EmiliaViaene/Un-designing-a-Thermal-Prediction-System/documentation/images/IMG_2420.jpg

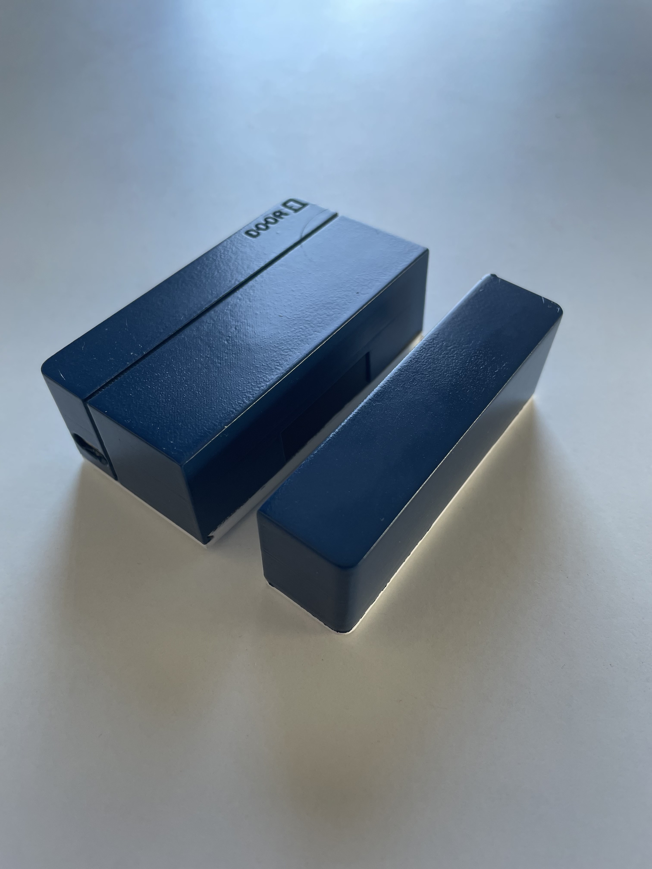
documentation/images/IMG_2420.jpg
