EmiliaViaene/Un-designing-a-Thermal-Prediction-System/documentation/images/IMG_2422.jpg

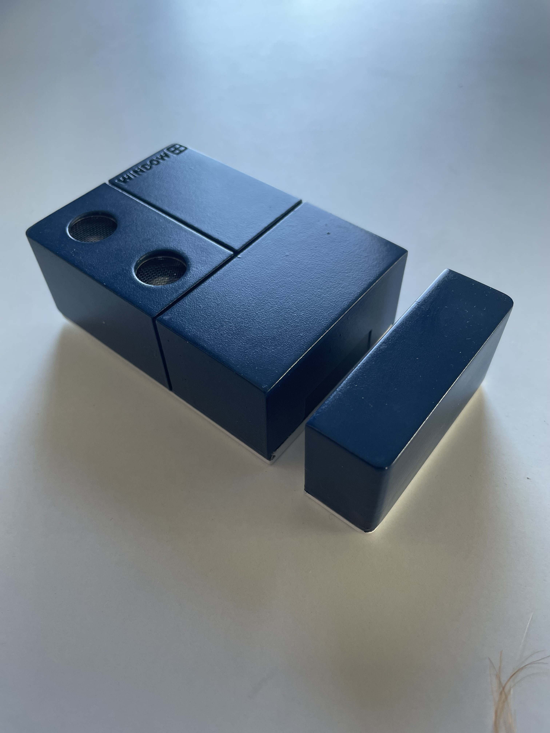
documentation/images/IMG_2422.jpg
