EmiliaViaene/Un-designing-a-Thermal-Prediction-System/documentation/images/IMG_2423.jpg

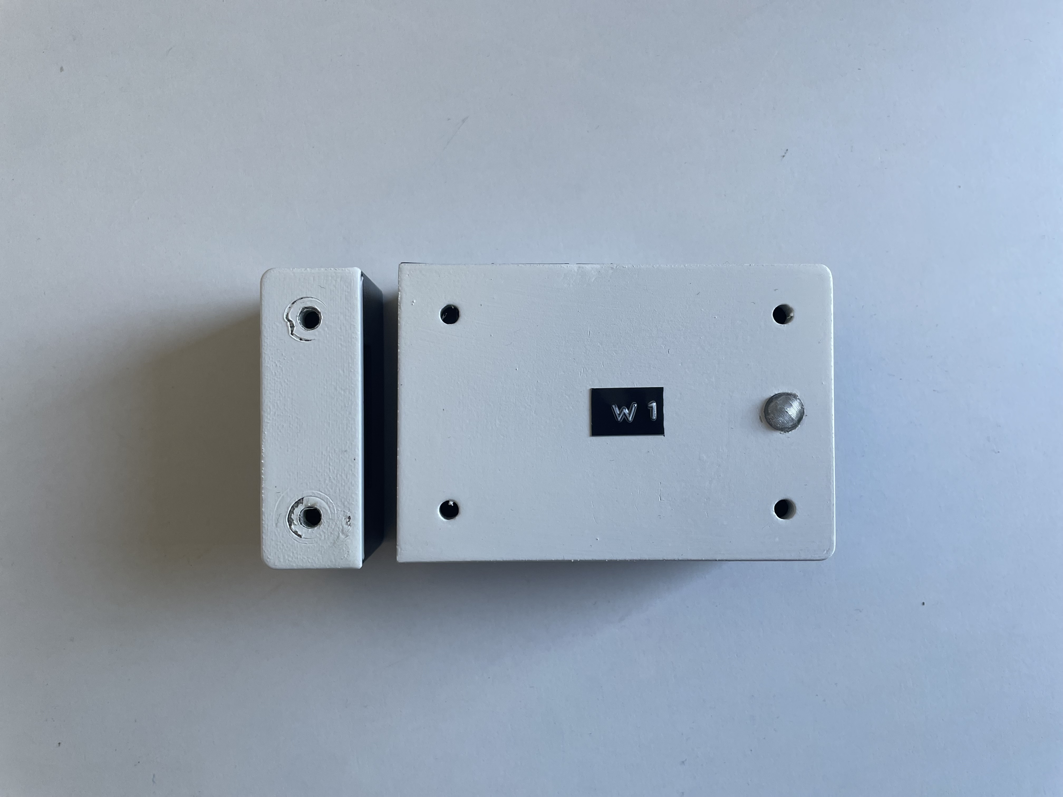
documentation/images/IMG_2423.jpg
