EmiliaViaene/Un-designing-a-Thermal-Prediction-System/documentation/images/IMG_2436.jpg

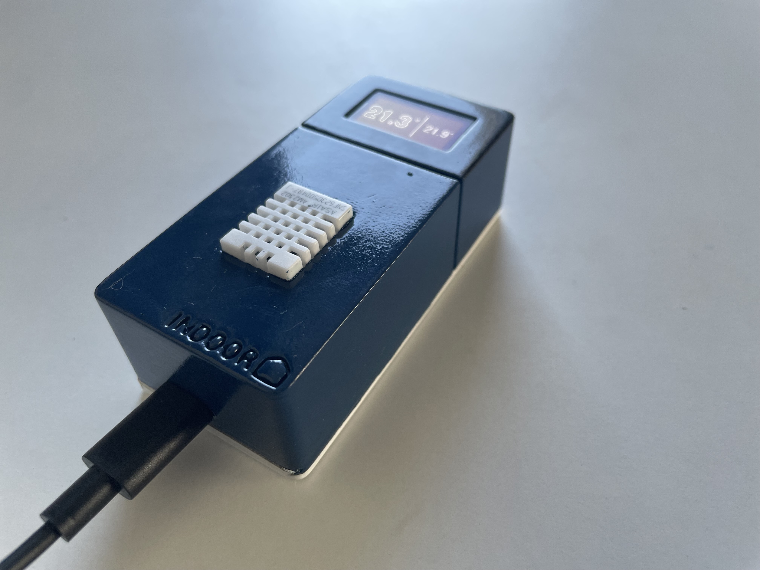
documentation/images/IMG_2436.jpg
