EmiliaViaene/Un-designing-a-Thermal-Prediction-System/documentation/images/IMG_2437.jpg

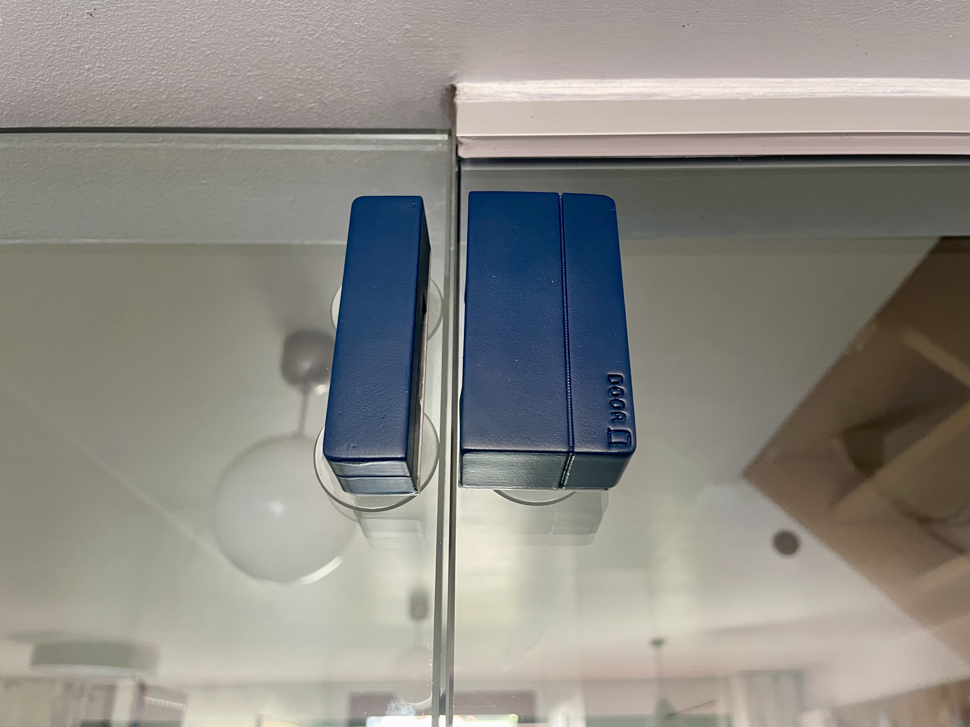
documentation/images/IMG_2437.jpg
