EmiliaViaene/Un-designing-a-Thermal-Prediction-System/documentation/images/IMG_2438.jpg

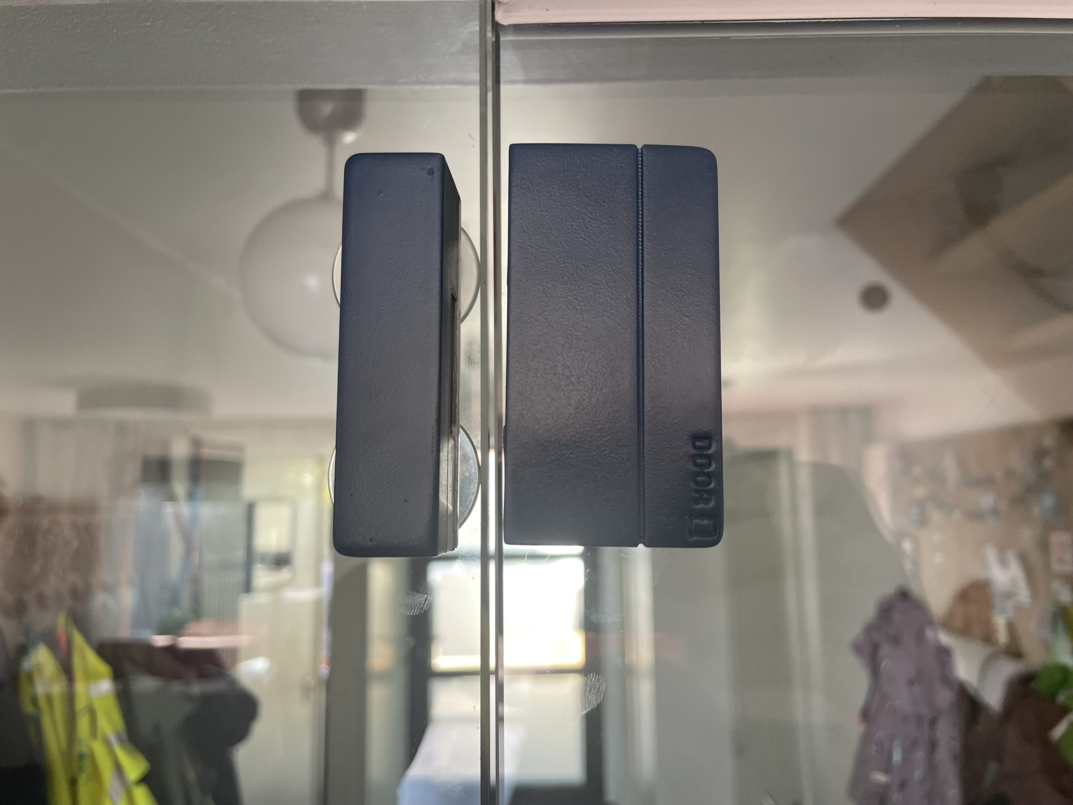
documentation/images/IMG_2438.jpg
