EmiliaViaene/Un-designing-a-Thermal-Prediction-System/documentation/images/IMG_2439.jpg

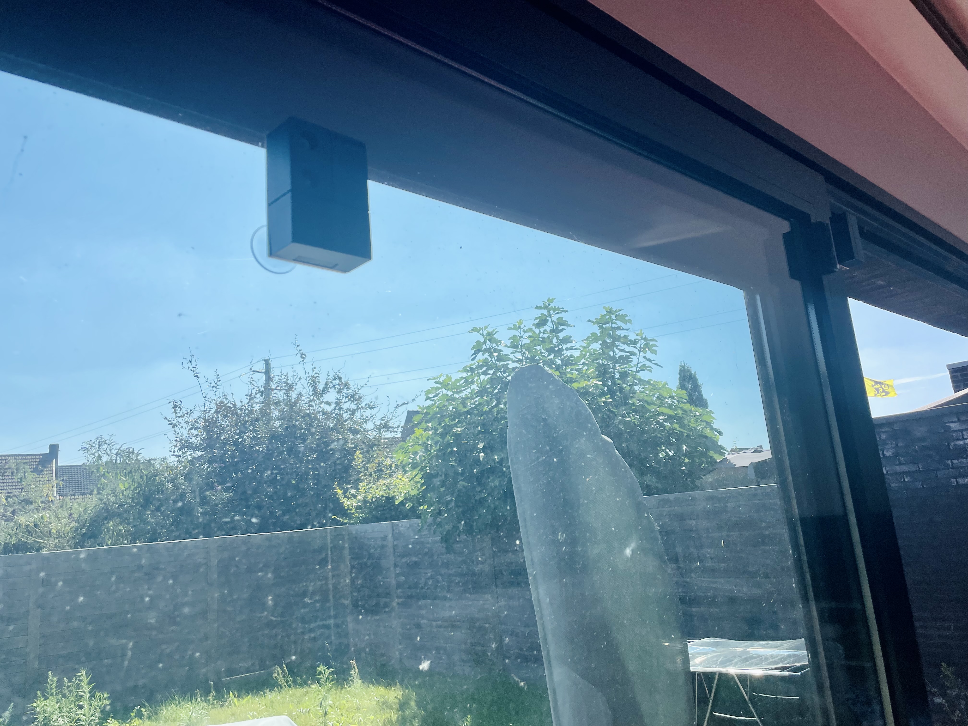
documentation/images/IMG_2439.jpg
