EmiliaViaene/Un-designing-a-Thermal-Prediction-System/documentation/images/IMG_2440.jpg

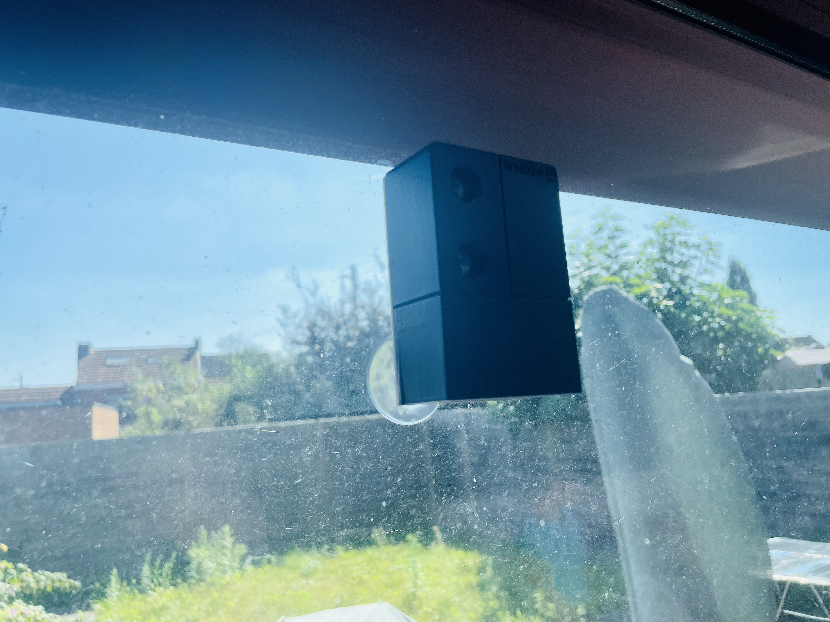
documentation/images/IMG_2440.jpg
