EmiliaViaene/Un-designing-a-Thermal-Prediction-System/documentation/images/IMG_2441.jpg

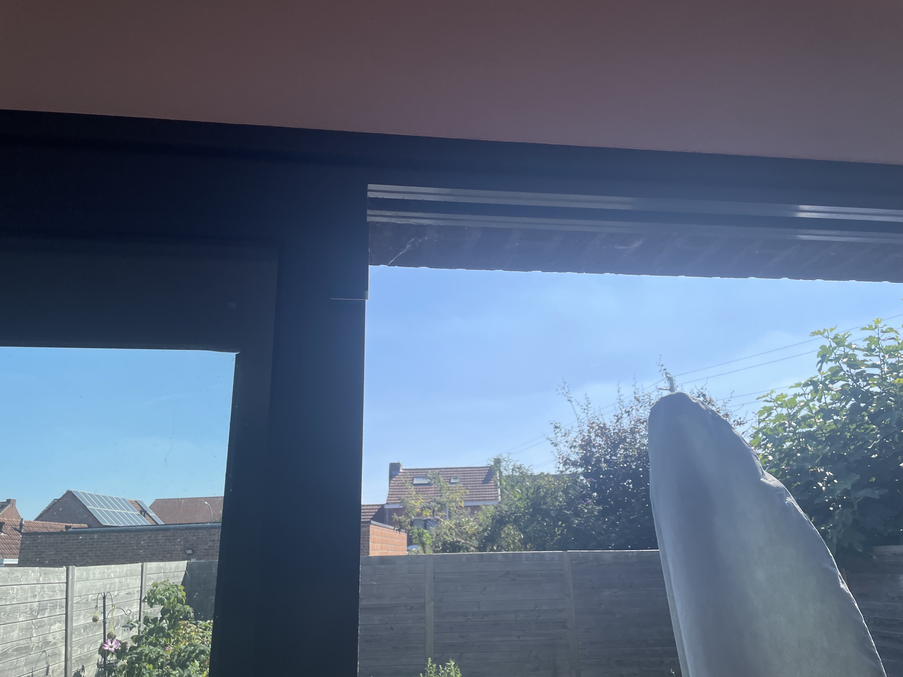
documentation/images/IMG_2441.jpg
