EmiliaViaene/Un-designing-a-Thermal-Prediction-System/documentation/images/IMG_2443.jpg

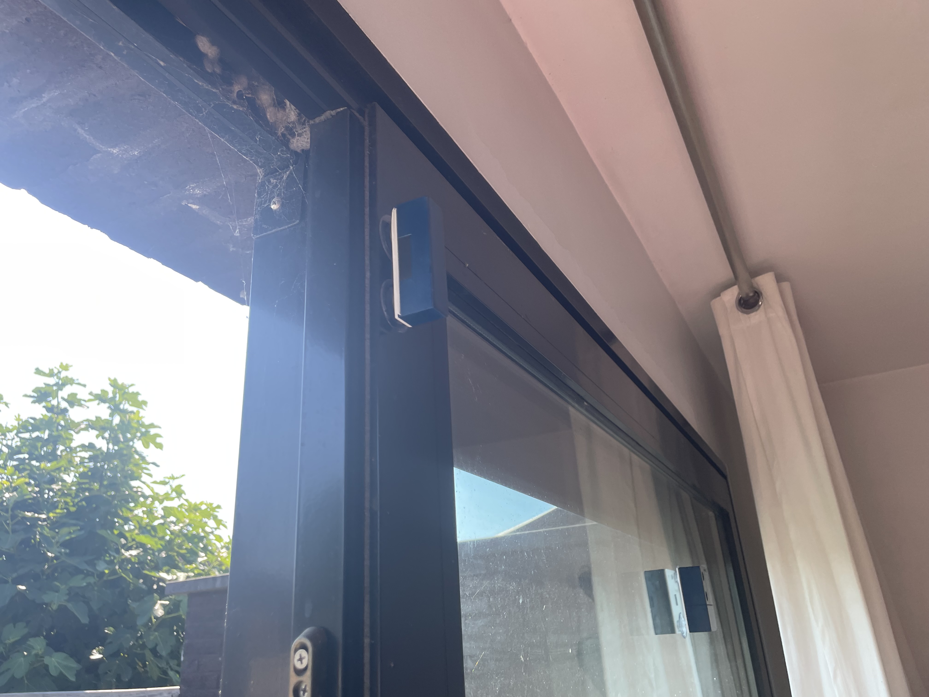
documentation/images/IMG_2443.jpg
