EmiliaViaene/Un-designing-a-Thermal-Prediction-System/documentation/images/IMG_2444.jpg

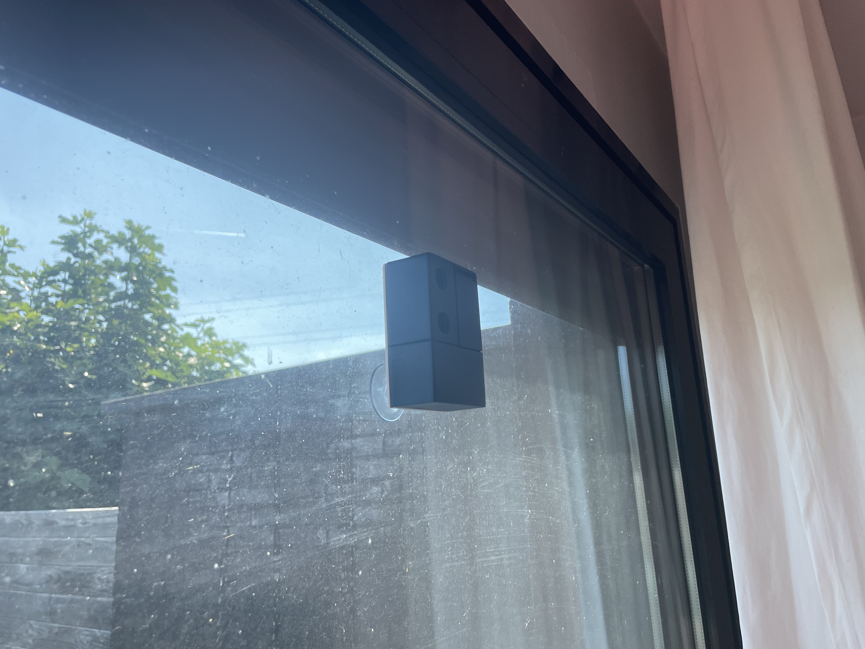
documentation/images/IMG_2444.jpg
