EmiliaViaene/Un-designing-a-Thermal-Prediction-System/documentation/images/IMG_2445.jpg

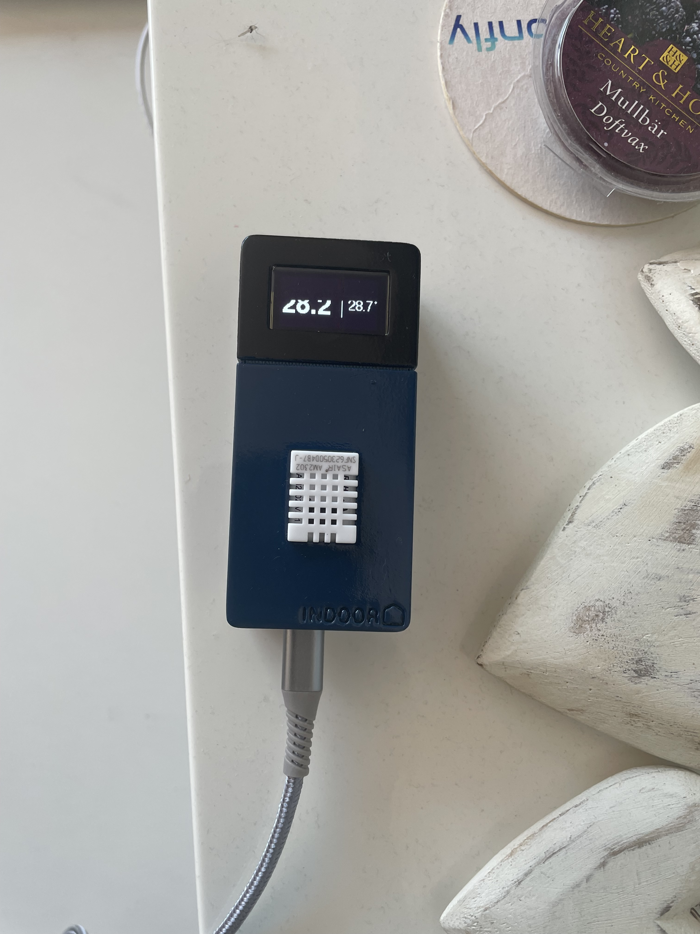
documentation/images/IMG_2445.jpg
