EmiliaViaene/Un-designing-a-Thermal-Prediction-System/documentation/images/IMG_2470.jpg

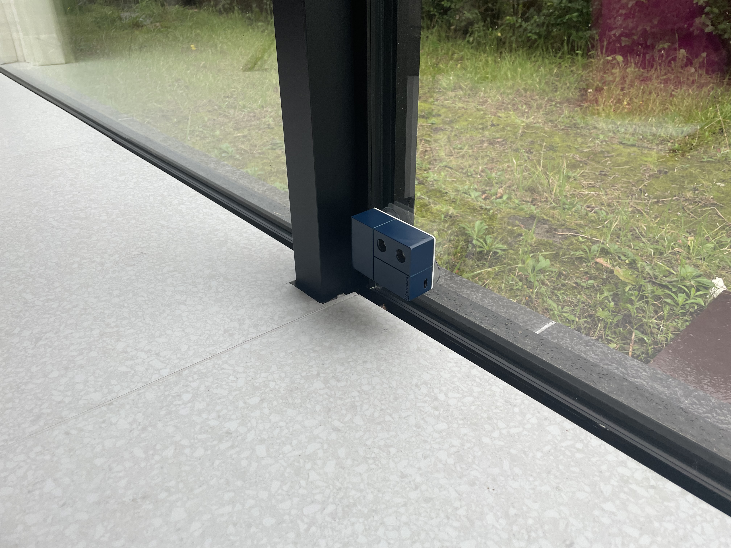
documentation/images/IMG_2470.jpg
