EmiliaViaene/Un-designing-a-Thermal-Prediction-System/documentation/images/IMG_2471.jpg

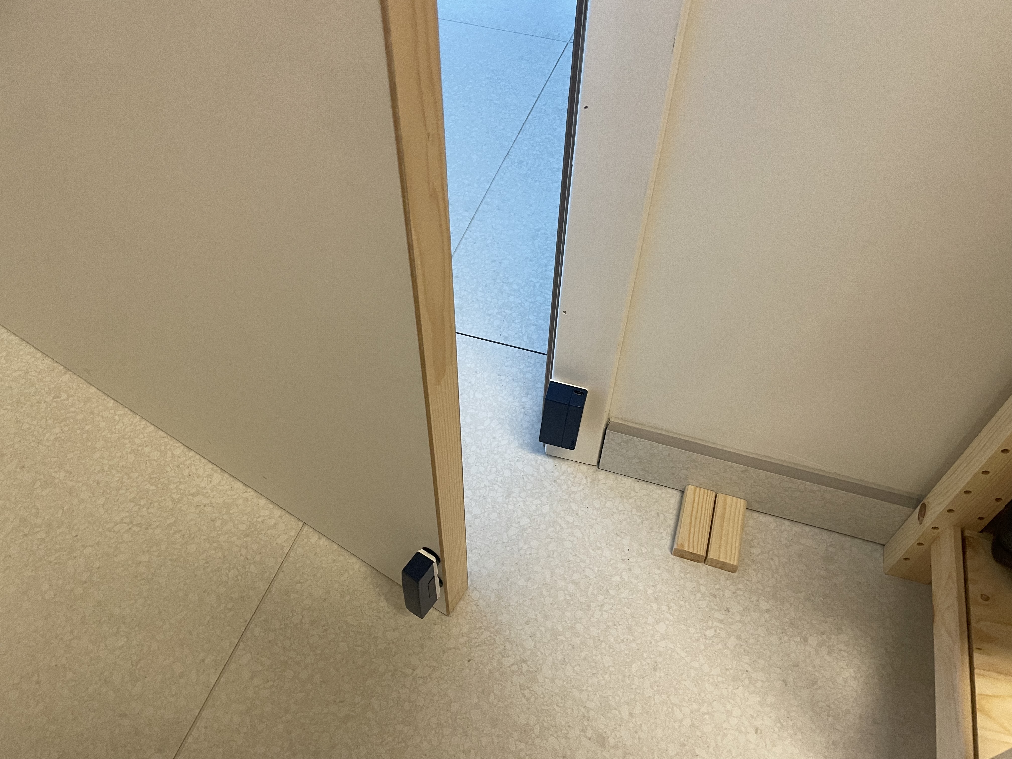
documentation/images/IMG_2471.jpg
