EmiliaViaene/Un-designing-a-Thermal-Prediction-System/documentation/images/IMG_2472.jpg

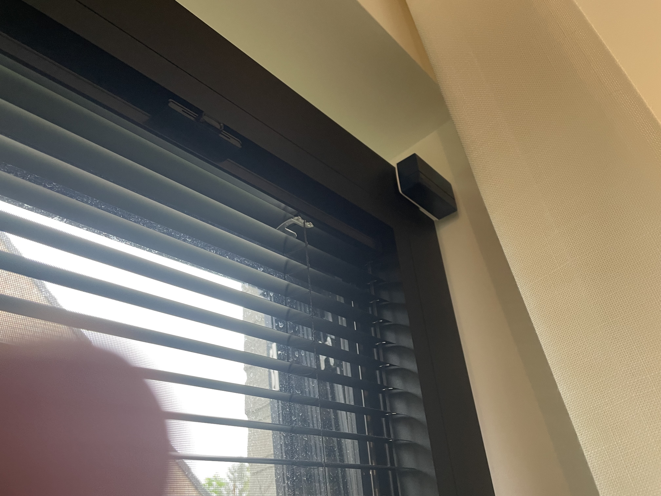
documentation/images/IMG_2472.jpg
