EmiliaViaene/Un-designing-a-Thermal-Prediction-System/documentation/images/IMG_2473.jpg

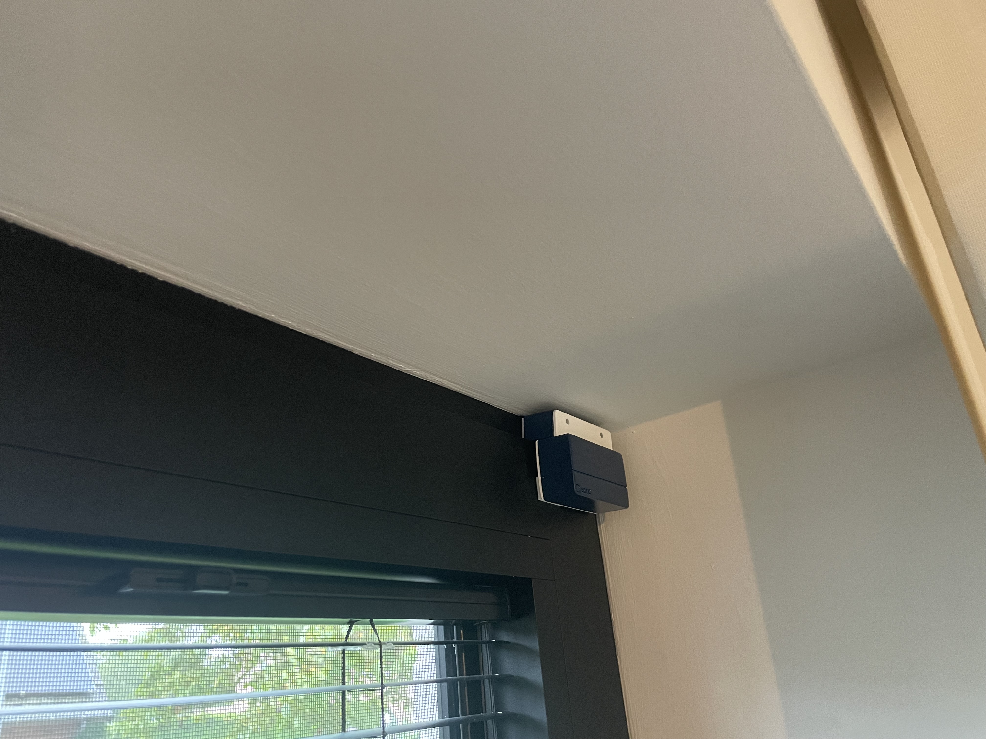
documentation/images/IMG_2473.jpg
