EmiliaViaene/Un-designing-a-Thermal-Prediction-System/documentation/images/IMG_2474.jpg

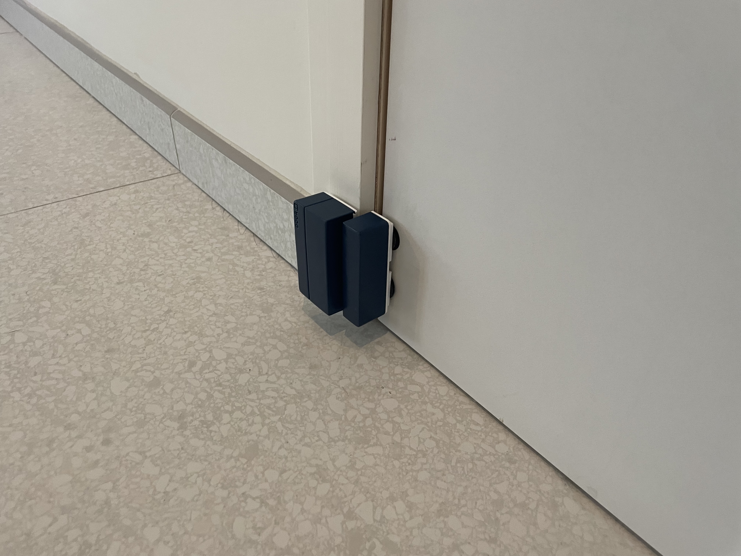
documentation/images/IMG_2474.jpg
