EmiliaViaene/Un-designing-a-Thermal-Prediction-System/documentation/images/IMG_2487.jpg

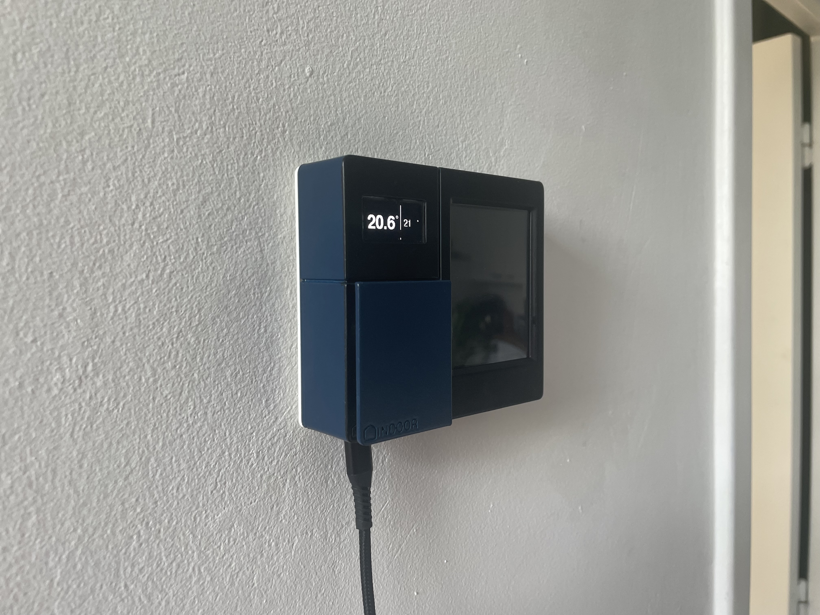
documentation/images/IMG_2487.jpg
