EmiliaViaene/Un-designing-a-Thermal-Prediction-System/documentation/images/IMG_2490.jpg

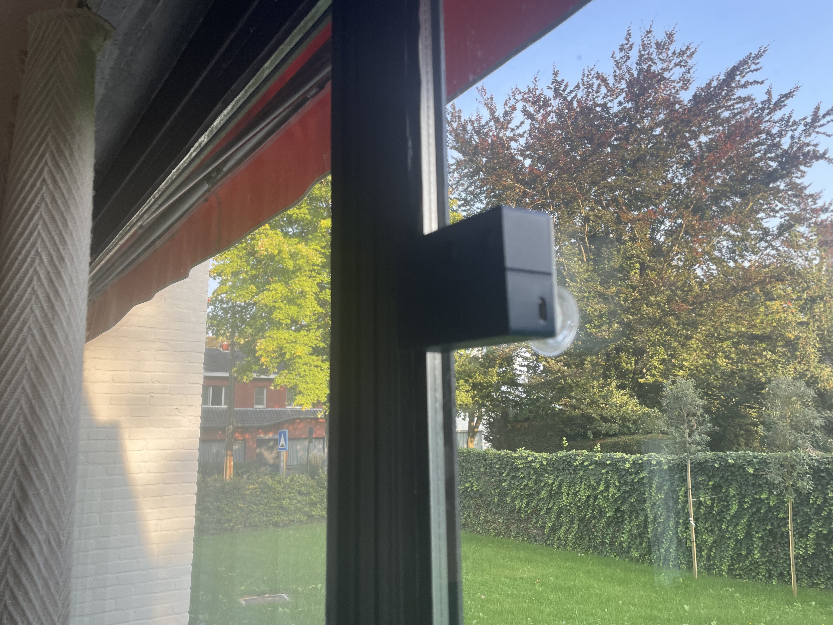
documentation/images/IMG_2490.jpg
