EmiliaViaene/Un-designing-a-Thermal-Prediction-System/documentation/images/IMG_2494.jpg

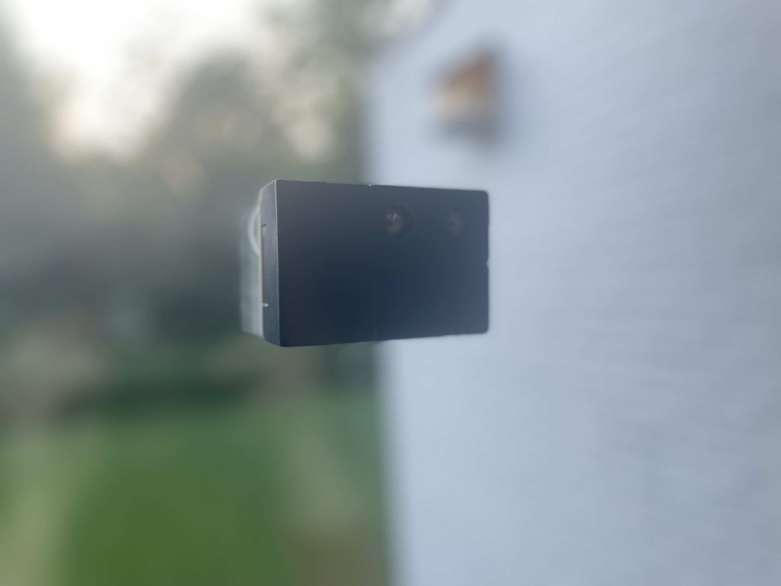
documentation/images/IMG_2494.jpg
