EmiliaViaene/Un-designing-a-Thermal-Prediction-System/documentation/images/IMG_2496.jpg

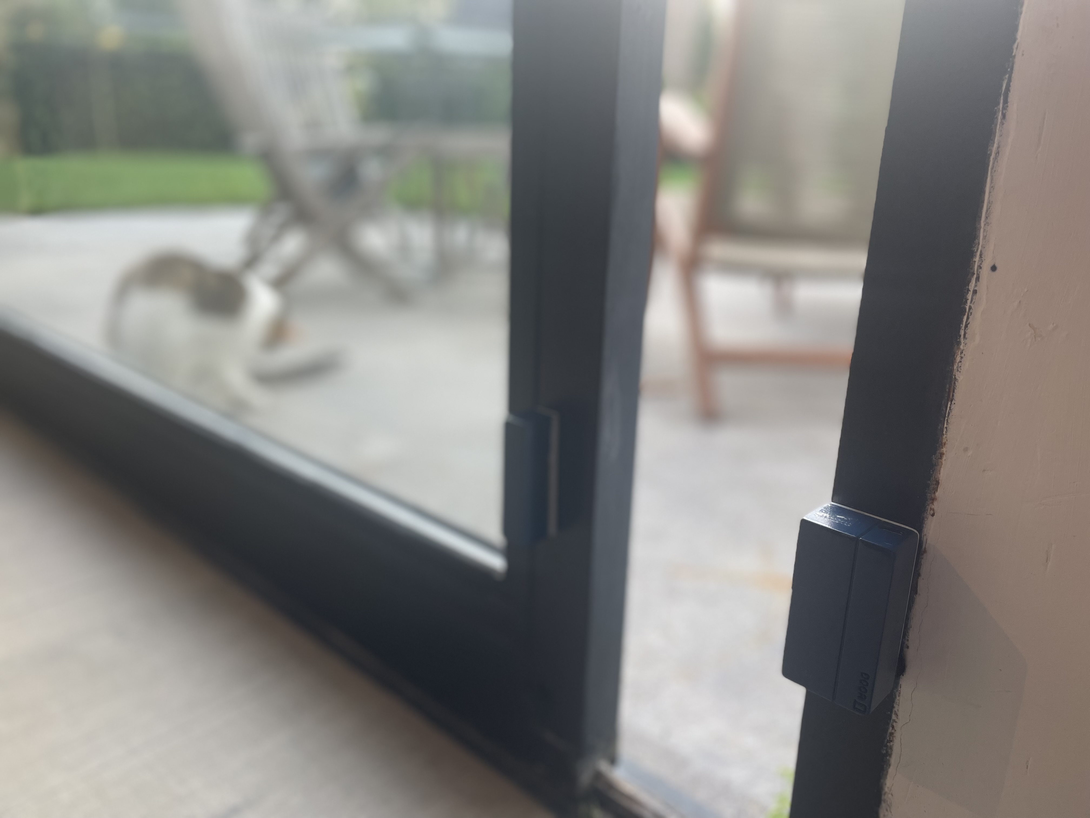
documentation/images/IMG_2496.jpg
