EmiliaViaene/Un-designing-a-Thermal-Prediction-System/documentation/images/IMG_2497.jpg

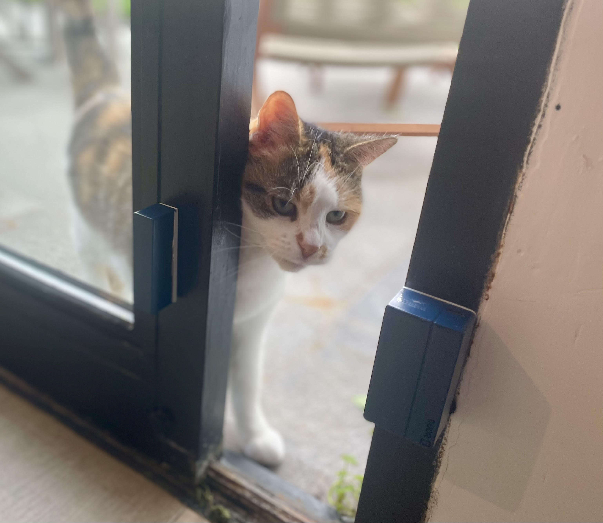
documentation/images/IMG_2497.jpg
