EmiliaViaene/Un-designing-a-Thermal-Prediction-System/documentation/images/IMG_2499.jpg

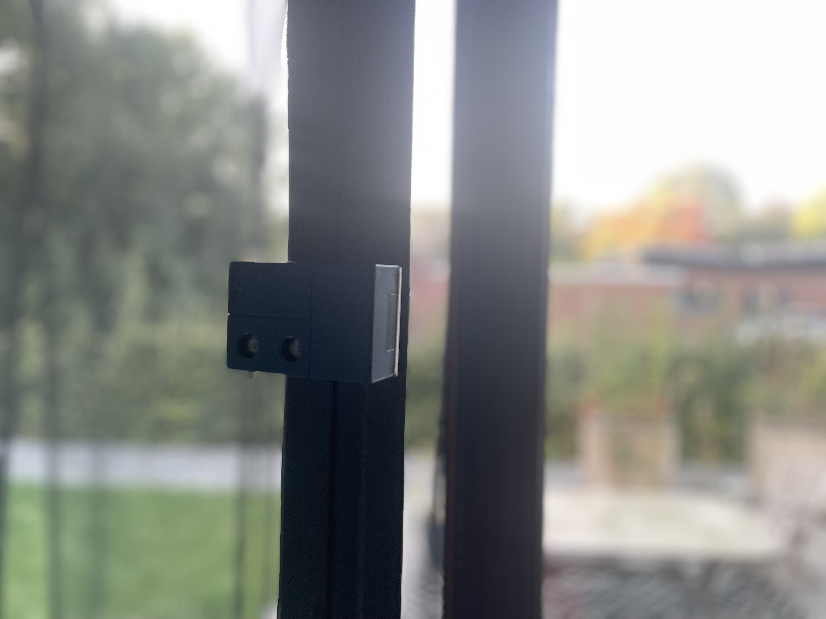
documentation/images/IMG_2499.jpg
