EmiliaViaene/Un-designing-a-Thermal-Prediction-System/documentation/images/IMG_2507.jpg

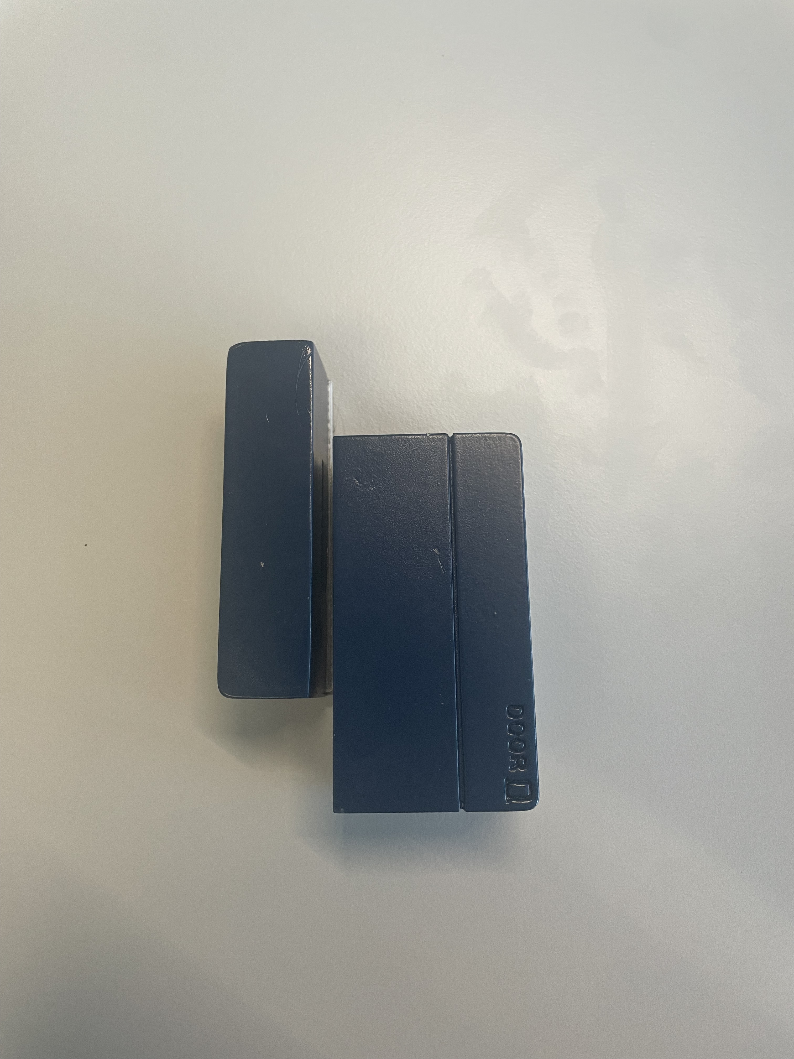
documentation/images/IMG_2507.jpg
