EmiliaViaene/Un-designing-a-Thermal-Prediction-System/documentation/images/IMG_2514.jpg

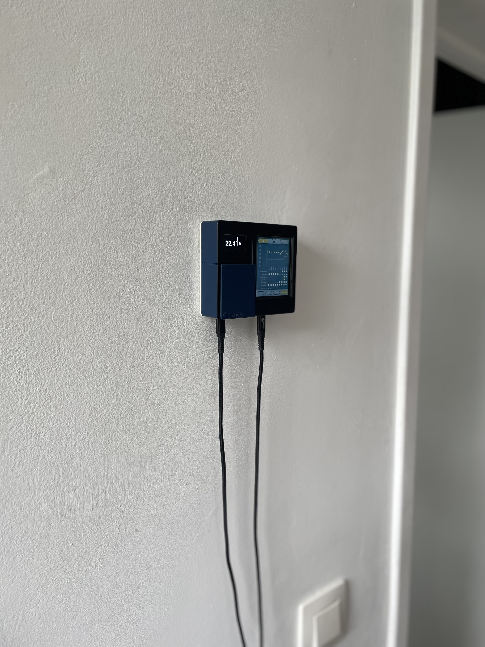
documentation/images/IMG_2514.jpg
