EmiliaViaene/Un-designing-a-Thermal-Prediction-System/documentation/images/IMG_2515.jpg

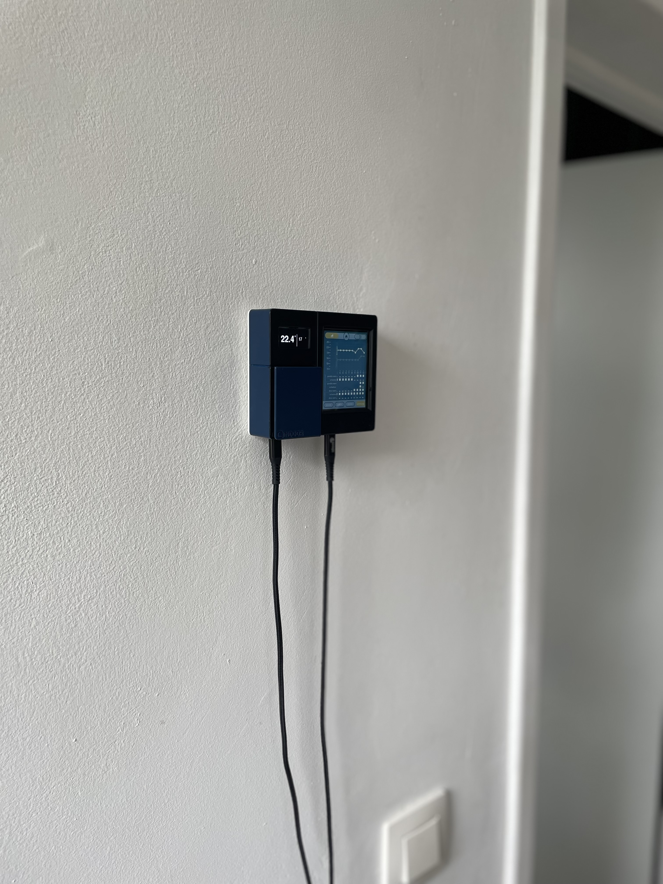
documentation/images/IMG_2515.jpg
