EmiliaViaene/Un-designing-a-Thermal-Prediction-System/documentation/images/IMG_2520.jpg

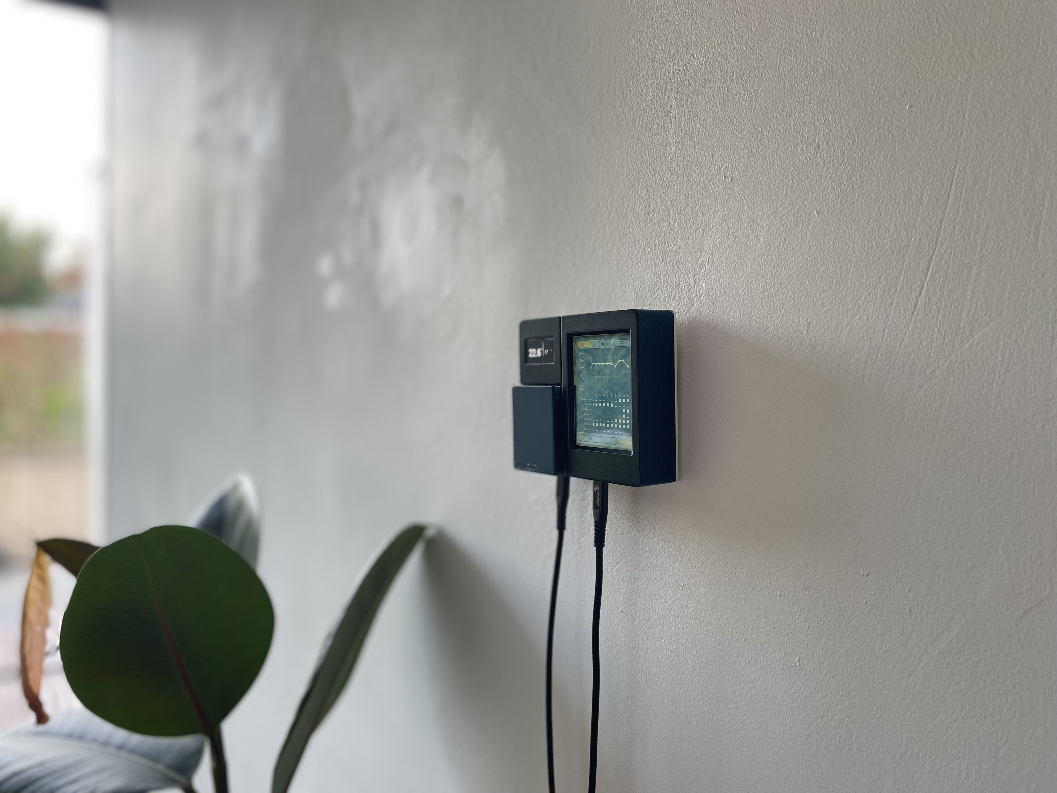
documentation/images/IMG_2520.jpg
