EmiliaViaene/Un-designing-a-Thermal-Prediction-System/documentation/images/IMG_2523.jpg

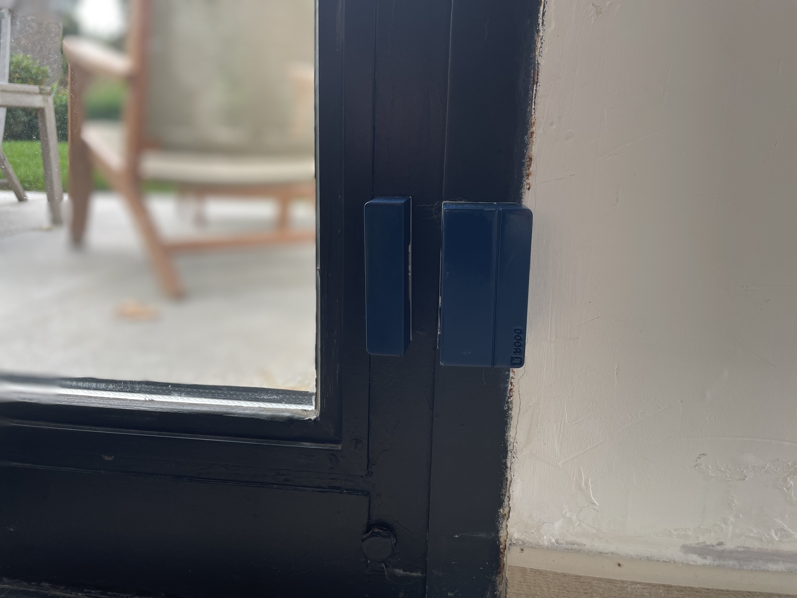
documentation/images/IMG_2523.jpg
