EmiliaViaene/Un-designing-a-Thermal-Prediction-System/documentation/images/IMG_2535.jpg

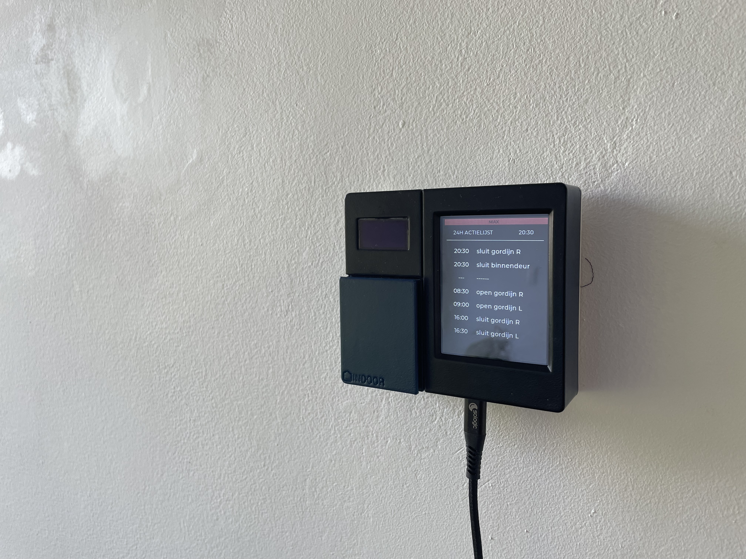
documentation/images/IMG_2535.jpg
