EmiliaViaene/Un-designing-a-Thermal-Prediction-System/documentation/images/IMG_2536.jpg

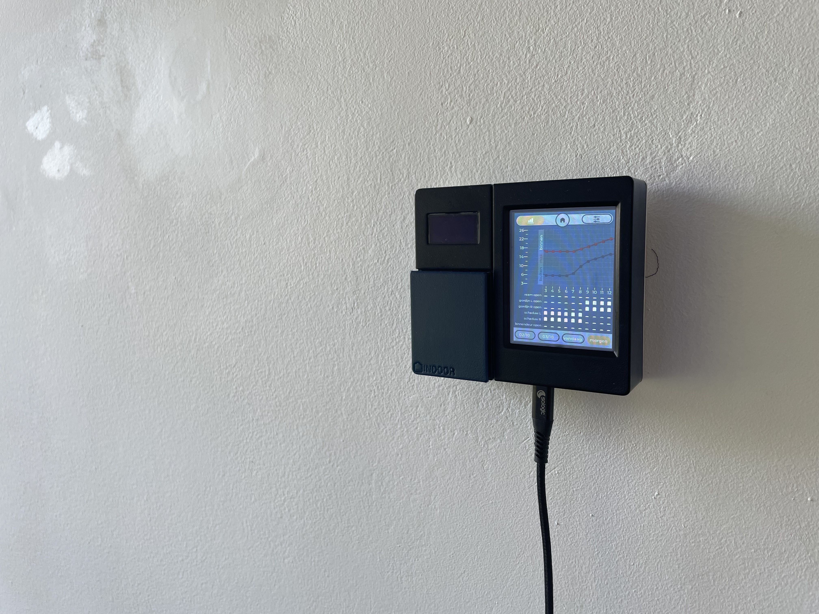
documentation/images/IMG_2536.jpg
