EmiliaViaene/Un-designing-a-Thermal-Prediction-System/documentation/images/IMG_2537.jpg

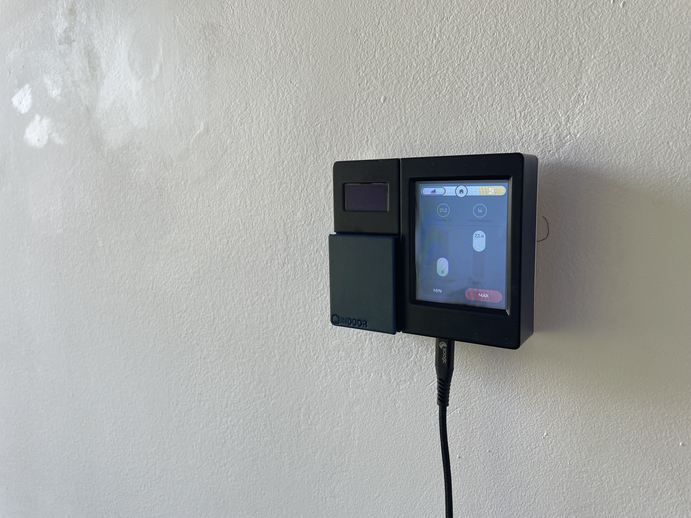
documentation/images/IMG_2537.jpg
