EmiliaViaene/Un-designing-a-Thermal-Prediction-System/documentation/images/IMG_3441.jpg

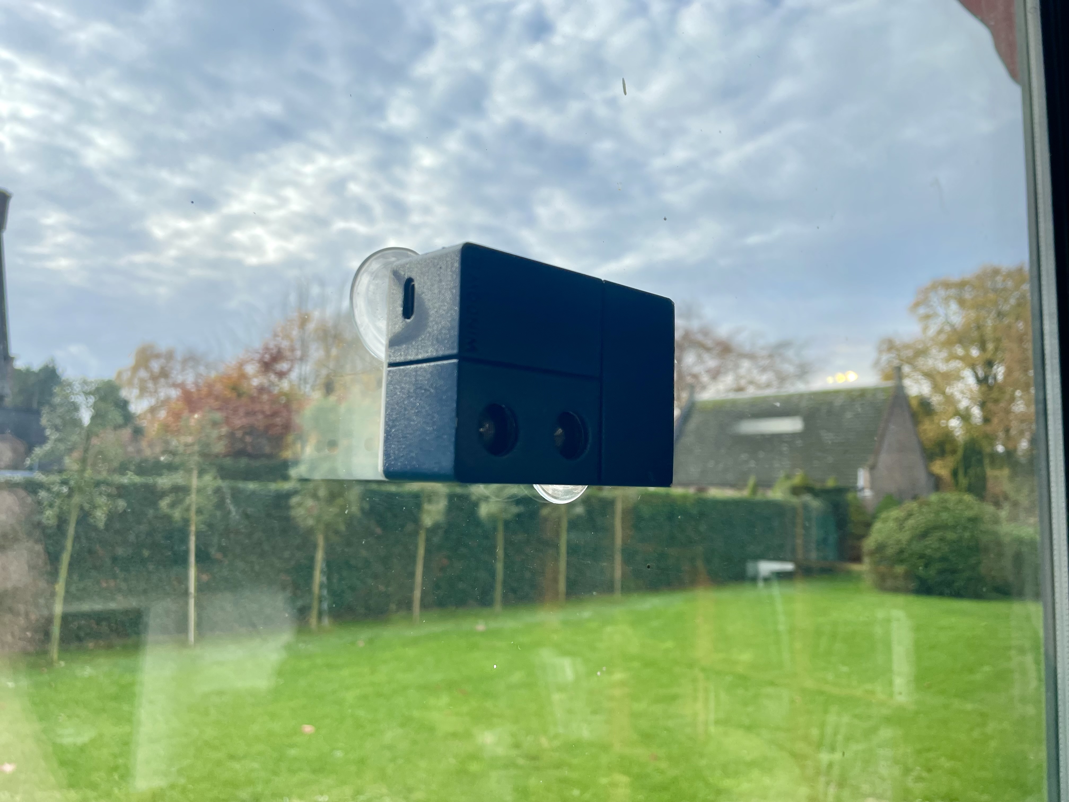
documentation/images/IMG_3441.jpg
