EmiliaViaene/Un-designing-a-Thermal-Prediction-System/documentation/images/IMG_3460_edited.jpg

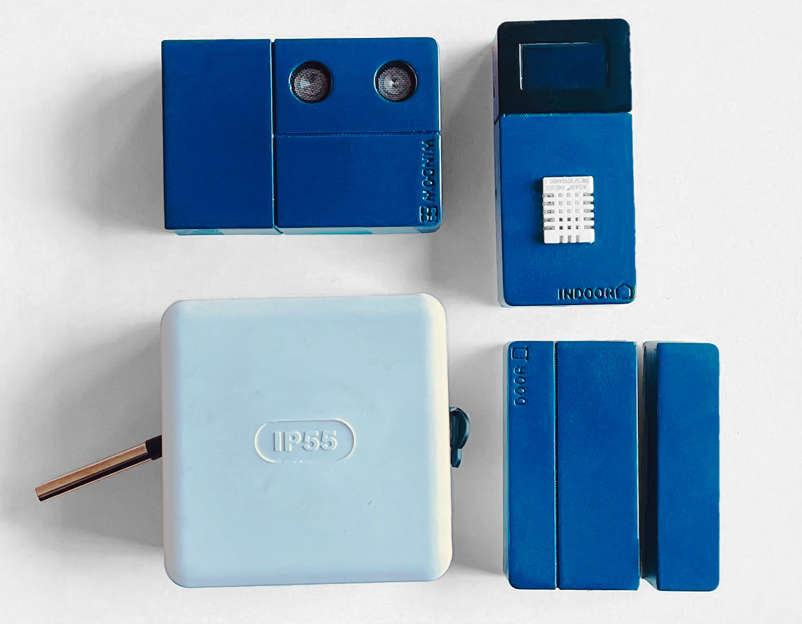
documentation/images/IMG_3460_edited.jpg
