EmiliaViaene/Un-designing-a-Thermal-Prediction-System/documentation/images/IMG_3574.jpg

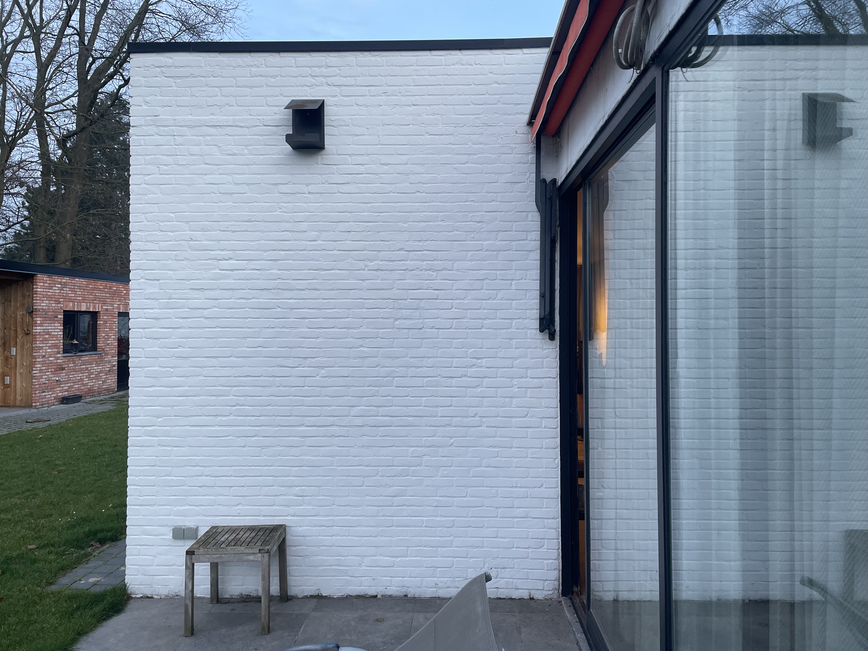
documentation/images/IMG_3574.jpg
