EmiliaViaene/Un-designing-a-Thermal-Prediction-System/documentation/images/IMG_3576.jpg

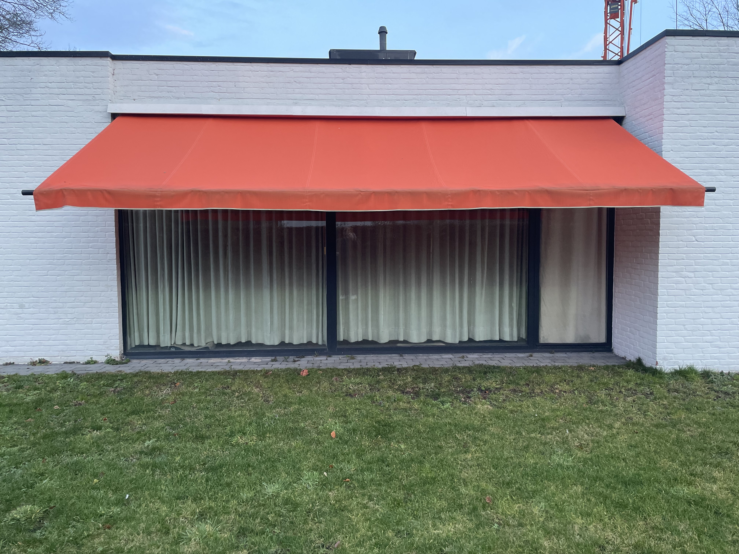
documentation/images/IMG_3576.jpg
