EmiliaViaene/Un-designing-a-Thermal-Prediction-System/documentation/recruitment/CoolAI_flyer.jpg

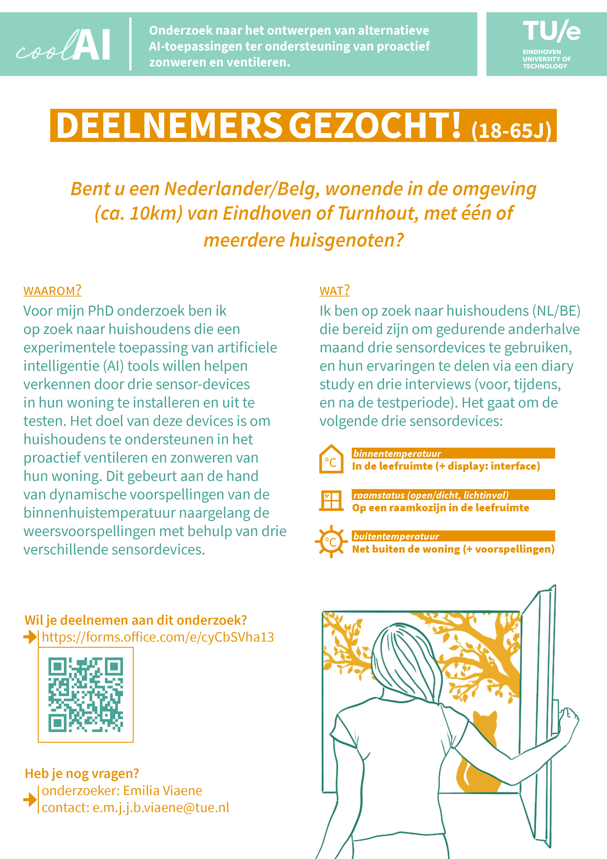
documentation/recruitment/CoolAI_flyer.jpg
