EmiliaViaene/Un-designing-a-Thermal-Prediction-System/hardware/3D_print_files/window-sensor/windowbox.SLDASM

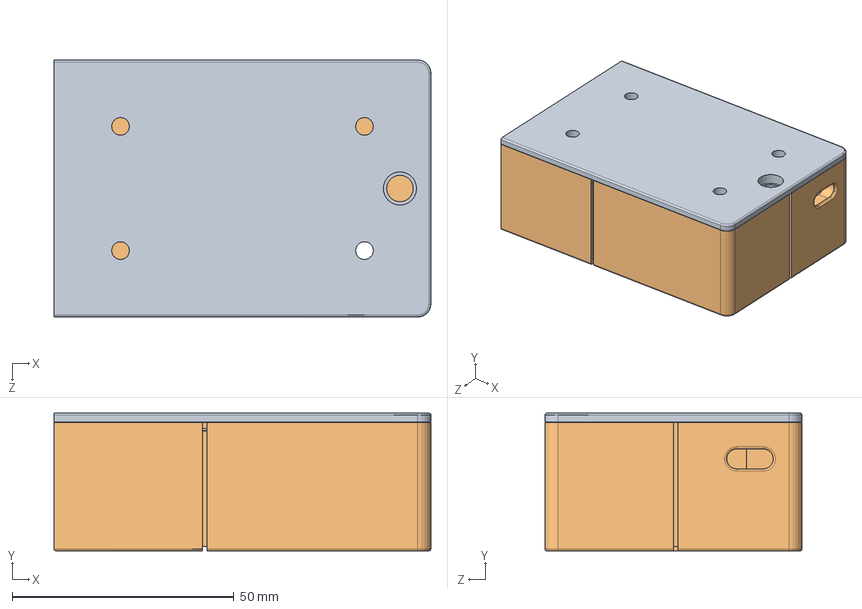
[picture p48: CAD file, 2026-08-19]
hardware/3D_print_files/window-sensor/windowbox.SLDASM
85.0 x 31.1 x 58.0 mm
windowbox_V2
sliding-lid_V2
