EmiliaViaene/Un-designing-a-Thermal-Prediction-System/hardware/3D_print_files/window-sensor/reed (magnet) box/MAGNET_windowbox_V2.SLDPRT

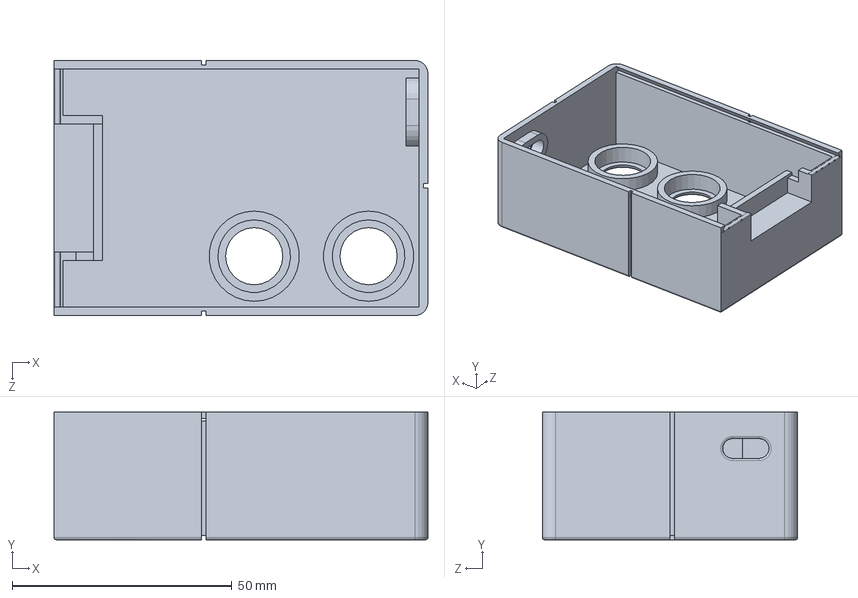
[picture p61: CAD file, 2026-08-19]
hardware/3D_print_files/window-sensor/reed (magnet) box/MAGNET_windowbox_V2.SLDPRT
85.0 x 29.0 x 58.0 mm
