EmiliaViaene/Un-designing-a-Thermal-Prediction-System/hardware/3D_print_files/CYD interface/cyd_box.SLDPRT

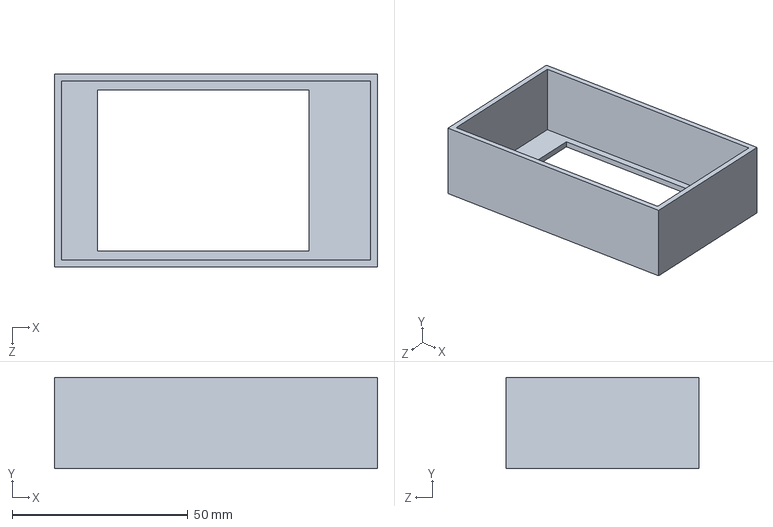
[picture p62: CAD file, 2026-08-19]
hardware/3D_print_files/CYD interface/cyd_box.SLDPRT
92.0 x 26.0 x 55.0 mm
