EmiliaViaene/Un-designing-a-Thermal-Prediction-System/hardware/3D_print_files/window-sensor/sliding-lid_V2.SLDPRT

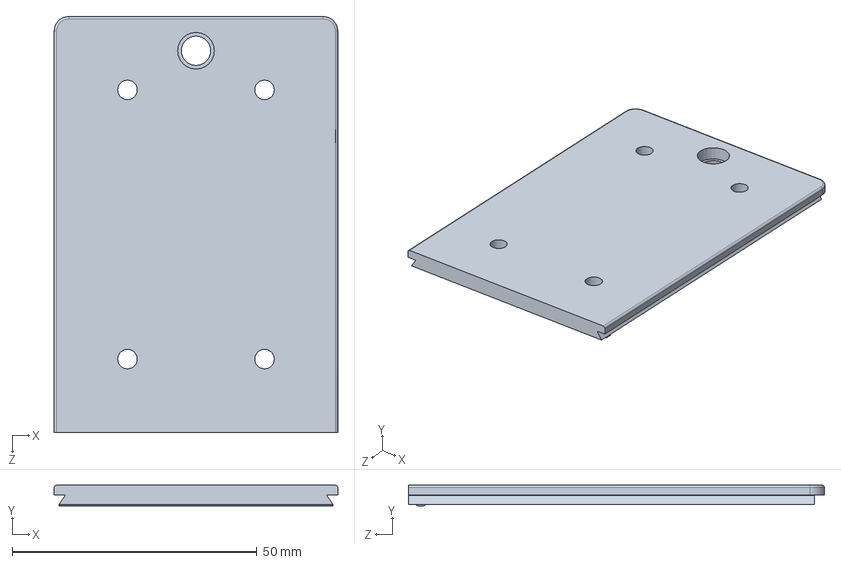
[picture p63: CAD file, 2026-08-19]
hardware/3D_print_files/window-sensor/sliding-lid_V2.SLDPRT
58.0 x 4.20 x 85.0 mm
