EmiliaViaene/Un-designing-a-Thermal-Prediction-System/hardware/3D_print_files/Indoor/Indoor.SLDASM

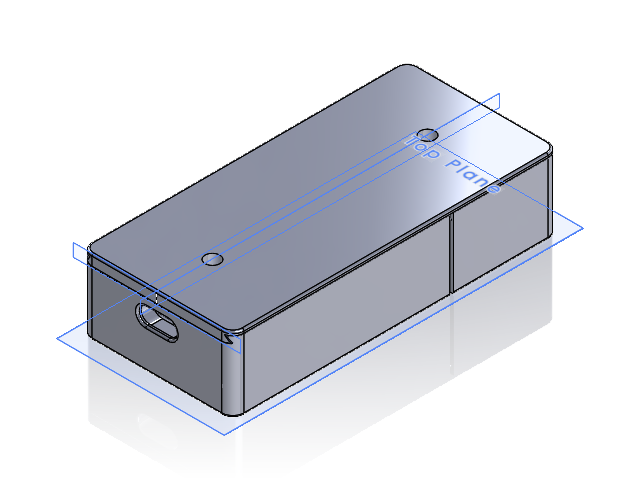
[picture p64: CAD file, 2026-08-19]
hardware/3D_print_files/Indoor/Indoor.SLDASM
Indoor_box
Indoor_lid
