EmiliaViaene/Un-designing-a-Thermal-Prediction-System/data/API/API_solar_radiance/API_solarmeasurements(september_H2).csv

straling | ts
0 | 2024-09-01 00:00:00
0 | 2024-09-01 01:00:00
0 | 2024-09-01 02:00:00
0 | 2024-09-01 03:00:00
0 | 2024-09-01 04:00:00
13 | 2024-09-01 05:00:00
36 | 2024-09-01 06:00:00
52 | 2024-09-01 07:00:00
140 | 2024-09-01 08:00:00
226 | 2024-09-01 09:00:00
242 | 2024-09-01 10:00:00
248 | 2024-09-01 11:00:00
242 | 2024-09-01 12:00:00
213 | 2024-09-01 13:00:00
171 | 2024-09-01 14:00:00
120 | 2024-09-01 15:00:00
74 | 2024-09-01 16:00:00
26 | 2024-09-01 17:00:00
1 | 2024-09-01 18:00:00
0 | 2024-09-01 19:00:00
0 | 2024-09-01 20:00:00
0 | 2024-09-01 21:00:00
0 | 2024-09-01 22:00:00
0 | 2024-09-01 23:00:00
0 | 2024-09-02 00:00:00
0 | 2024-09-02 01:00:00
0 | 2024-09-02 02:00:00
0 | 2024-09-02 03:00:00
0 | 2024-09-02 04:00:00
16 | 2024-09-02 05:00:00
55 | 2024-09-02 06:00:00
110 | 2024-09-02 07:00:00
168 | 2024-09-02 08:00:00
189 | 2024-09-02 09:00:00
238 | 2024-09-02 10:00:00
215 | 2024-09-02 11:00:00
197 | 2024-09-02 12:00:00
171 | 2024-09-02 13:00:00
122 | 2024-09-02 14:00:00
84 | 2024-09-02 15:00:00
38 | 2024-09-02 16:00:00
18 | 2024-09-02 17:00:00
2 | 2024-09-02 18:00:00
0 | 2024-09-02 19:00:00
0 | 2024-09-02 20:00:00
0 | 2024-09-02 21:00:00
0 | 2024-09-02 22:00:00
0 | 2024-09-02 23:00:00
0 | 2024-09-03 00:00:00
0 | 2024-09-03 01:00:00
0 | 2024-09-03 02:00:00
0 | 2024-09-03 03:00:00
0 | 2024-09-03 04:00:00
12 | 2024-09-03 05:00:00
26 | 2024-09-03 06:00:00
43 | 2024-09-03 07:00:00
63 | 2024-09-03 08:00:00
75 | 2024-09-03 09:00:00
114 | 2024-09-03 10:00:00
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
27 | 2024-09-30 12:00:00
54 | 2024-09-30 13:00:00
32 | 2024-09-30 14:00:00
19 | 2024-09-30 15:00:00
6 | 2024-09-30 16:00:00
0 | 2024-09-30 17:00:00
0 | 2024-09-30 18:00:00
0 | 2024-09-30 19:00:00
0 | 2024-09-30 20:00:00
0 | 2024-09-30 21:00:00
0 | 2024-09-30 22:00:00
0 | 2024-09-30 23:00:00
