EmiliaViaene/Un-designing-a-Thermal-Prediction-System/code/interface_UI_code/H1/ui_HH1/ui_HH1.ino

#include <lvgl.h>
#include <TFT_eSPI.h>
#include <XPT2046_Touchscreen.h>
#include <ui.h>

#include <WiFi.h>
#include <HTTPClient.h>
#include <Arduino_JSON.h>

/*Don't forget to set Sketchbook location in File/Preferences to the path of your UI project (the parent foder of this INO file)*/

///////////////////////////////////////////////////////////////////////// init wifi and declare Http vars
const char* ssid = "Proximus-Home-92F0";
// Password of your Wifi network.
const char* password = "w9bdkm3hjhm6p";

// const char* ssid = "VFNL-DF7B08";
// //Password of your Wifi network.
// const char* password = "4W8DNSU424SP4";

// For a final application, check the API call limits per hour/minute to avoid getting blocked/banned
unsigned long lastTime = 10001;
unsigned long firstTime = 0;
// Timer set to 1 minutes (60000)
unsigned long timerDelay = 10000;
String jsonBuffer;
String httpGETRequest(const char* serverName) {
  WiFiClient client;
  HTTPClient http;
  // Your Domain name with URL path or IP address with path
  http.begin(client, serverName);
  // Send HTTP POST request
  int httpResponseCode = http.GET();
  String payload = "{}"; 
  if (httpResponseCode>0) {
    Serial.print("HTTP Response code: ");
    Serial.println(httpResponseCode);
    payload = http.getString();
  }
  else {
    Serial.print("Error code: ");
    Serial.println(httpResponseCode);
  }
  // Free resources
  http.end();
  return payload;
}

// Touchscreen pins
#define XPT2046_IRQ 36   // T_IRQ
#define XPT2046_MOSI 32  // T_DIN
#define XPT2046_MISO 39  // T_OUT
#define XPT2046_CLK 25   // T_CLK
#define XPT2046_CS 33    // T_CS

SPIClass touchscreenSPI = SPIClass(VSPI);
XPT2046_Touchscreen touchscreen(XPT2046_CS, XPT2046_IRQ);

#define SCREEN_WIDTH 240
#define SCREEN_HEIGHT 320
TFT_eSPI tft = TFT_eSPI();  //Added to be able to rotate the screen

// Touchscreen coordinates: (x, y) and pressure (z)
int x, y, z;

#define DRAW_BUF_SIZE (SCREEN_WIDTH * SCREEN_HEIGHT / 10 * (LV_COLOR_DEPTH / 8))
uint32_t draw_buf[DRAW_BUF_SIZE / 4];

// If logging is enabled, it will inform the user about what is happening in the library
void log_print(lv_log_level_t level, const char * buf) {
  LV_UNUSED(level);
  Serial.println(buf);
  Serial.flush();
}

// Get the Touchscreen data
void touchscreen_read(lv_indev_t * indev, lv_indev_data_t * data) {
  // Checks if Touchscreen was touched, and prints X, Y and Pressure (Z)
  if(touchscreen.tirqTouched() && touchscreen.touched()) {
    // Get Touchscreen points
    TS_Point p = touchscreen.getPoint();
    // Calibrate Touchscreen points with map function to the correct width and height
    x = map(p.x, 200, 3700, 1, SCREEN_WIDTH);
    y = map(p.y, 240, 3800, 1, SCREEN_HEIGHT);
    z = p.z;

    data->state = LV_INDEV_STATE_PRESSED;

    // Set the coordinates
    data->point.x = x;
    data->point.y = y;
  }
  else {
    data->state = LV_INDEV_STATE_RELEASED;
  }
}

/*Set tick routine needed for LVGL internal timings*/
static uint32_t my_tick_get_cb (void) { return millis(); }


///////////////////////////////////////////////////////////////////// date labels on history tab /////////////////////////////////////////////////////////////////////
void gisteren_setdatelabels(lv_event_t * e) {
  String serverPath = "http://data.id.tue.nl/datasets/downloadPublic/json/VXBLaG9hNmUyUzIweGtlSVVJdkh0aHhDOVU1blI0TUNYeG9Ib1ZGT2RhST0=";
  jsonBuffer = httpGETRequest(serverPath.c_str());
  Serial.println(jsonBuffer);
  JSONVar myObject = JSON.parse(jsonBuffer);
  // JSON.typeof(jsonVar) can be used to get the type of the var
  if (JSON.typeof(myObject) == "undefined") {
    Serial.println("Parsing input failed!");
    return;
  }
  lv_label_set_text(ui_NAN_RAAM_OOST, "");
  lv_label_set_text(ui_NAN_RAAM_WEST, "");
  lv_label_set_text(ui_NAN_GORDIJN_OOST, "");
  lv_label_set_text(ui_NAN_GORDIJN_WEST, "");
  lv_label_set_text(ui_NAN_SCHADUW_OOST, "");
  lv_label_set_text(ui_NAN_SCHADUW_WEST, "");

  lv_label_set_text(ui_GISTEREN_DAGKEUZE_LABEL1, myObject[0]["date_threedaysago"]);
  lv_label_set_text(ui_GISTEREN_DAGKEUZE_LABEL2, myObject[0]["date_twodaysago"]);
  lv_label_set_text(ui_GISTEREN_DAGKEUZE_LABEL3, myObject[0]["date_yesterday"]);
  // set values to 0
  for (int i = 0; i < 24; i++) {
    lv_chart_series_t * ui_GISTEREN_CHART_BUITEN_TEMPERATUUR_series_1 = lv_chart_get_series_next(ui_GISTEREN_CHART_BUITEN_TEMPERATUUR, NULL);
    lv_chart_set_next_value(ui_GISTEREN_CHART_BUITEN_TEMPERATUUR, ui_GISTEREN_CHART_BUITEN_TEMPERATUUR_series_1, 0);
    lv_chart_series_t * ui_GISTEREN_CHART_BINNEN_TEMPERATUUR_series_1 = lv_chart_get_series_next(ui_GISTEREN_CHART_BINNEN_TEMPERATUUR, NULL);
    lv_chart_set_next_value(ui_GISTEREN_CHART_BINNEN_TEMPERATUUR, ui_GISTEREN_CHART_BINNEN_TEMPERATUUR_series_1, 0);
    lv_chart_series_t * ui_GISTEREN_CHART_RAAM_OOST_series_1 = lv_chart_get_series_next(ui_GISTEREN_CHART_RAAM_OOST, NULL);
    lv_chart_set_next_value(ui_GISTEREN_CHART_RAAM_OOST, ui_GISTEREN_CHART_RAAM_OOST_series_1, 0);
    lv_chart_series_t * ui_GISTEREN_CHART_RAAM_WEST_series_1 = lv_chart_get_series_next(ui_GISTEREN_CHART_RAAM_WEST, NULL);
    lv_chart_set_next_value(ui_GISTEREN_CHART_RAAM_WEST, ui_GISTEREN_CHART_RAAM_WEST_series_1, 0);    
    lv_chart_series_t * ui_GISTEREN_CHART_GORDIJN_OOST_series_1 = lv_chart_get_series_next(ui_GISTEREN_CHART_GORDIJN_OOST, NULL);
    lv_chart_set_next_value(ui_GISTEREN_CHART_GORDIJN_OOST, ui_GISTEREN_CHART_GORDIJN_OOST_series_1, 0);
    lv_chart_series_t * ui_GISTEREN_CHART_GORDIJN_WEST_series_1 = lv_chart_get_series_next(ui_GISTEREN_CHART_GORDIJN_WEST, NULL);
    lv_chart_set_next_value(ui_GISTEREN_CHART_GORDIJN_WEST, ui_GISTEREN_CHART_GORDIJN_WEST_series_1, 0);    
    lv_chart_series_t * ui_GISTEREN_CHART_SCHADUW_OOST_series_1_array = lv_chart_get_series_next(ui_GISTEREN_CHART_SCHADUW_OOST, NULL);
    lv_chart_set_next_value(ui_GISTEREN_CHART_SCHADUW_OOST, ui_GISTEREN_CHART_SCHADUW_OOST_series_1_array, 0);
    lv_chart_series_t * ui_GISTEREN_CHART_SCHADUW_WEST_series_1 = lv_chart_get_series_next(ui_GISTEREN_CHART_SCHADUW_WEST, NULL);
    lv_chart_set_next_value(ui_GISTEREN_CHART_SCHADUW_WEST, ui_GISTEREN_CHART_SCHADUW_WEST_series_1, 0);
  }
}

///////////////////////////////////////////////////////////////////// set values for three days ago /////////////////////////////////////////////////////////////////////
void gisteren_setvalues_1(lv_event_t * e) {
  String serverPath = "http://data.id.tue.nl/datasets/downloadPublic/json/NXYrY2dJL0hyNE4xVG1kVzdJcTdrdUJ0ZkEwdFY2dDJSbDM0bDJWZXM4RT0=";
  jsonBuffer = httpGETRequest(serverPath.c_str());
  Serial.println(jsonBuffer);
  JSONVar myObject = JSON.parse(jsonBuffer);
  // JSON.typeof(jsonVar) can be used to get the type of the var
  if (JSON.typeof(myObject) == "undefined") {
    Serial.println("Parsing input failed!");
    return;
  }
  //set the range for the temperature charts
  int mintemp = (double) myObject[0]["pp1"];
  int maxtemp = (double) myObject[0]["pp2"];
  lv_scale_set_range(ui_GISTEREN_CHART_BUITEN_TEMPERATUUR_Yaxis1,  mintemp, maxtemp);
  lv_scale_set_range(ui_GISTEREN_CHART_BUITEN_TEMPERATUUR_Yaxis2,  mintemp, maxtemp);
  lv_scale_set_range(ui_GISTEREN_CHART_BINNEN_TEMPERATUUR_Yaxis1,  mintemp, maxtemp);
  lv_scale_set_range(ui_GISTEREN_CHART_BINNEN_TEMPERATUUR_Yaxis2,  mintemp, maxtemp);
  lv_scale_set_range(ui_GISTEREN_CHART_TEMPERATUUR_LABELS_Yaxis1,  mintemp, maxtemp);
  lv_scale_set_range(ui_GISTEREN_CHART_TEMPERATUUR_LABELS_Yaxis2,  mintemp, maxtemp);
  lv_chart_set_range(ui_GISTEREN_CHART_BUITEN_TEMPERATUUR, LV_CHART_AXIS_PRIMARY_Y, mintemp, maxtemp);
  lv_chart_set_range(ui_GISTEREN_CHART_BUITEN_TEMPERATUUR, LV_CHART_AXIS_SECONDARY_Y, mintemp, maxtemp);
  lv_chart_set_range(ui_GISTEREN_CHART_BINNEN_TEMPERATUUR, LV_CHART_AXIS_PRIMARY_Y, mintemp, maxtemp);
  lv_chart_set_range(ui_GISTEREN_CHART_BINNEN_TEMPERATUUR, LV_CHART_AXIS_SECONDARY_Y, mintemp, maxtemp);
  lv_chart_set_range(ui_GISTEREN_CHART_TEMPERATUUR_LABELS, LV_CHART_AXIS_PRIMARY_Y, mintemp, maxtemp);
  lv_chart_set_range(ui_GISTEREN_CHART_TEMPERATUUR_LABELS, LV_CHART_AXIS_SECONDARY_Y, mintemp, maxtemp);

  lv_label_set_text(ui_NAN_RAAM_OOST, myObject[18]["NaN_times"]);
  lv_label_set_text(ui_NAN_RAAM_WEST, myObject[19]["NaN_times"]);
  lv_label_set_text(ui_NAN_GORDIJN_OOST, myObject[20]["NaN_times"]);
  lv_label_set_text(ui_NAN_GORDIJN_WEST, myObject[21]["NaN_times"]);
  lv_label_set_text(ui_NAN_SCHADUW_OOST, myObject[22]["NaN_times"]);
  lv_label_set_text(ui_NAN_SCHADUW_WEST, myObject[23]["NaN_times"]);

  //set values for the interface charts (voor = oost; achter = west)
  for (int i = 0; i < 24; i++) {
    lv_chart_series_t * ui_GISTEREN_CHART_BUITEN_TEMPERATUUR_series_1 = lv_chart_get_series_next(ui_GISTEREN_CHART_BUITEN_TEMPERATUUR, NULL);
    lv_chart_set_next_value(ui_GISTEREN_CHART_BUITEN_TEMPERATUUR, ui_GISTEREN_CHART_BUITEN_TEMPERATUUR_series_1, (double) myObject[i]["Temperature_outdoor"]);
    lv_chart_series_t * ui_GISTEREN_CHART_BINNEN_TEMPERATUUR_series_1 = lv_chart_get_series_next(ui_GISTEREN_CHART_BINNEN_TEMPERATUUR, NULL);
    lv_chart_set_next_value(ui_GISTEREN_CHART_BINNEN_TEMPERATUUR, ui_GISTEREN_CHART_BINNEN_TEMPERATUUR_series_1, (double) myObject[i]["Temperature_indoor"]);
    lv_chart_series_t * ui_GISTEREN_CHART_RAAM_OOST_series_1 = lv_chart_get_series_next(ui_GISTEREN_CHART_RAAM_OOST, NULL);
    lv_chart_set_next_value(ui_GISTEREN_CHART_RAAM_OOST, ui_GISTEREN_CHART_RAAM_OOST_series_1, (double) myObject[i]["windowdoor_voor"]);
    lv_chart_series_t * ui_GISTEREN_CHART_RAAM_WEST_series_1 = lv_chart_get_series_next(ui_GISTEREN_CHART_RAAM_WEST, NULL);
    lv_chart_set_next_value(ui_GISTEREN_CHART_RAAM_WEST, ui_GISTEREN_CHART_RAAM_WEST_series_1, (double) myObject[i]["windowdoor_achter"]);
    lv_chart_series_t * ui_GISTEREN_CHART_GORDIJN_OOST_series_1 = lv_chart_get_series_next(ui_GISTEREN_CHART_GORDIJN_OOST, NULL);
    lv_chart_set_next_value(ui_GISTEREN_CHART_GORDIJN_OOST, ui_GISTEREN_CHART_GORDIJN_OOST_series_1, (double) myObject[i]["curtain_voor"]);
    lv_chart_series_t * ui_GISTEREN_CHART_GORDIJN_WEST_series_1 = lv_chart_get_series_next(ui_GISTEREN_CHART_GORDIJN_WEST, NULL);
    lv_chart_set_next_value(ui_GISTEREN_CHART_GORDIJN_WEST, ui_GISTEREN_CHART_GORDIJN_WEST_series_1, (double) myObject[i]["curtain_achter"]);
    lv_chart_series_t * ui_GISTEREN_CHART_SCHADUW_OOST_series_1_array = lv_chart_get_series_next(ui_GISTEREN_CHART_SCHADUW_OOST, NULL);
    lv_chart_set_next_value(ui_GISTEREN_CHART_SCHADUW_OOST, ui_GISTEREN_CHART_SCHADUW_OOST_series_1_array, (double) myObject[i]["shade_voor"]);
    lv_chart_series_t * ui_GISTEREN_CHART_SCHADUW_WEST_series_1 = lv_chart_get_series_next(ui_GISTEREN_CHART_SCHADUW_WEST, NULL);
    lv_chart_set_next_value(ui_GISTEREN_CHART_SCHADUW_WEST, ui_GISTEREN_CHART_SCHADUW_WEST_series_1, (double) myObject[i]["shade_achter"]);
  }
}

///////////////////////////////////////////////////////////////////// set values for two days ago /////////////////////////////////////////////////////////////////////
void gisteren_setvalues_2(lv_event_t * e) {
  // lv_refr_now(NULL);
  String serverPath = "http://data.id.tue.nl/datasets/downloadPublic/json/S0VDci9IdXlibEtQcFRTSUZhSVIxcC9GMVkydW94b2tuZWwvbUVrLzlxYz0=";
  jsonBuffer = httpGETRequest(serverPath.c_str());
  Serial.println(jsonBuffer);
  JSONVar myObject = JSON.parse(jsonBuffer);
  // JSON.typeof(jsonVar) can be used to get the type of the var
  if (JSON.typeof(myObject) == "undefined") {
    Serial.println("Parsing input failed!");
    return;
  }
  //set the range for the temperature charts
  int mintemp = (double) myObject[0]["pp1"];
  int maxtemp = (double) myObject[0]["pp2"];
  lv_scale_set_range(ui_GISTEREN_CHART_BUITEN_TEMPERATUUR_Yaxis1,  mintemp, maxtemp);
  lv_scale_set_range(ui_GISTEREN_CHART_BUITEN_TEMPERATUUR_Yaxis2,  mintemp, maxtemp);
  lv_scale_set_range(ui_GISTEREN_CHART_BINNEN_TEMPERATUUR_Yaxis1,  mintemp, maxtemp);
  lv_scale_set_range(ui_GISTEREN_CHART_BINNEN_TEMPERATUUR_Yaxis2,  mintemp, maxtemp);
  lv_scale_set_range(ui_GISTEREN_CHART_TEMPERATUUR_LABELS_Yaxis1,  mintemp, maxtemp);
  lv_scale_set_range(ui_GISTEREN_CHART_TEMPERATUUR_LABELS_Yaxis2,  mintemp, maxtemp);
  lv_chart_set_range(ui_GISTEREN_CHART_BUITEN_TEMPERATUUR, LV_CHART_AXIS_PRIMARY_Y, mintemp, maxtemp);
  lv_chart_set_range(ui_GISTEREN_CHART_BUITEN_TEMPERATUUR, LV_CHART_AXIS_SECONDARY_Y, mintemp, maxtemp);
  lv_chart_set_range(ui_GISTEREN_CHART_BINNEN_TEMPERATUUR, LV_CHART_AXIS_PRIMARY_Y, mintemp, maxtemp);
  lv_chart_set_range(ui_GISTEREN_CHART_BINNEN_TEMPERATUUR, LV_CHART_AXIS_SECONDARY_Y, mintemp, maxtemp);
  lv_chart_set_range(ui_GISTEREN_CHART_TEMPERATUUR_LABELS, LV_CHART_AXIS_PRIMARY_Y, mintemp, maxtemp);
  lv_chart_set_range(ui_GISTEREN_CHART_TEMPERATUUR_LABELS, LV_CHART_AXIS_SECONDARY_Y, mintemp, maxtemp);
  
  lv_label_set_text(ui_NAN_RAAM_OOST, myObject[18]["NaN_times"]);
  lv_label_set_text(ui_NAN_RAAM_WEST, myObject[19]["NaN_times"]);
  lv_label_set_text(ui_NAN_GORDIJN_OOST, myObject[20]["NaN_times"]);
  lv_label_set_text(ui_NAN_GORDIJN_WEST, myObject[21]["NaN_times"]);
  lv_label_set_text(ui_NAN_SCHADUW_OOST, myObject[22]["NaN_times"]);
  lv_label_set_text(ui_NAN_SCHADUW_WEST, myObject[23]["NaN_times"]);
  for (int i = 0; i < 24; i++) {
    lv_chart_series_t * ui_GISTEREN_CHART_BUITEN_TEMPERATUUR_series_1 = lv_chart_get_series_next(ui_GISTEREN_CHART_BUITEN_TEMPERATUUR, NULL);
    lv_chart_set_next_value(ui_GISTEREN_CHART_BUITEN_TEMPERATUUR, ui_GISTEREN_CHART_BUITEN_TEMPERATUUR_series_1, (double) myObject[i]["Temperature_outdoor"]);
    lv_chart_series_t * ui_GISTEREN_CHART_BINNEN_TEMPERATUUR_series_1 = lv_chart_get_series_next(ui_GISTEREN_CHART_BINNEN_TEMPERATUUR, NULL);
    lv_chart_set_next_value(ui_GISTEREN_CHART_BINNEN_TEMPERATUUR, ui_GISTEREN_CHART_BINNEN_TEMPERATUUR_series_1, (double) myObject[i]["Temperature_indoor"]);
    lv_chart_series_t * ui_GISTEREN_CHART_RAAM_OOST_series_1 = lv_chart_get_series_next(ui_GISTEREN_CHART_RAAM_OOST, NULL);
    lv_chart_set_next_value(ui_GISTEREN_CHART_RAAM_OOST, ui_GISTEREN_CHART_RAAM_OOST_series_1, (double) myObject[i]["windowdoor_voor"]);
    lv_chart_series_t * ui_GISTEREN_CHART_RAAM_WEST_series_1 = lv_chart_get_series_next(ui_GISTEREN_CHART_RAAM_WEST, NULL);
    lv_chart_set_next_value(ui_GISTEREN_CHART_RAAM_WEST, ui_GISTEREN_CHART_RAAM_WEST_series_1, (double) myObject[i]["windowdoor_achter"]);
    lv_chart_series_t * ui_GISTEREN_CHART_GORDIJN_OOST_series_1 = lv_chart_get_series_next(ui_GISTEREN_CHART_GORDIJN_OOST, NULL);
    lv_chart_set_next_value(ui_GISTEREN_CHART_GORDIJN_OOST, ui_GISTEREN_CHART_GORDIJN_OOST_series_1, (double) myObject[i]["curtain_voor"]);
    lv_chart_series_t * ui_GISTEREN_CHART_GORDIJN_WEST_series_1 = lv_chart_get_series_next(ui_GISTEREN_CHART_GORDIJN_WEST, NULL);
    lv_chart_set_next_value(ui_GISTEREN_CHART_GORDIJN_WEST, ui_GISTEREN_CHART_GORDIJN_WEST_series_1, (double) myObject[i]["curtain_achter"]);
    lv_chart_series_t * ui_GISTEREN_CHART_SCHADUW_OOST_series_1_array = lv_chart_get_series_next(ui_GISTEREN_CHART_SCHADUW_OOST, NULL);
    lv_chart_set_next_value(ui_GISTEREN_CHART_SCHADUW_OOST, ui_GISTEREN_CHART_SCHADUW_OOST_series_1_array, (double) myObject[i]["shade_voor"]);
    lv_chart_series_t * ui_GISTEREN_CHART_SCHADUW_WEST_series_1 = lv_chart_get_series_next(ui_GISTEREN_CHART_SCHADUW_WEST, NULL);
    lv_chart_set_next_value(ui_GISTEREN_CHART_SCHADUW_WEST, ui_GISTEREN_CHART_SCHADUW_WEST_series_1, (double) myObject[i]["shade_achter"]);
  }
}

///////////////////////////////////////////////////////////////////// set values for yesterday /////////////////////////////////////////////////////////////////////
void gisteren_setvalues_3(lv_event_t * e) {
  String serverPath = "http://data.id.tue.nl/datasets/downloadPublic/json/VXBLaG9hNmUyUzIweGtlSVVJdkh0aHhDOVU1blI0TUNYeG9Ib1ZGT2RhST0=";
  jsonBuffer = httpGETRequest(serverPath.c_str());
  Serial.println(jsonBuffer);
  JSONVar myObject = JSON.parse(jsonBuffer);
  // JSON.typeof(jsonVar) can be used to get the type of the var
  if (JSON.typeof(myObject) == "undefined") {
    Serial.println("Parsing input failed!");
    return;
  }
  //set the range for the temperature charts
  int mintemp = (double) myObject[0]["pp1"];
  int maxtemp = (double) myObject[0]["pp2"];
  lv_scale_set_range(ui_GISTEREN_CHART_BUITEN_TEMPERATUUR_Yaxis1,  mintemp, maxtemp);
  lv_scale_set_range(ui_GISTEREN_CHART_BUITEN_TEMPERATUUR_Yaxis2,  mintemp, maxtemp);
  lv_scale_set_range(ui_GISTEREN_CHART_BINNEN_TEMPERATUUR_Yaxis1,  mintemp, maxtemp);
  lv_scale_set_range(ui_GISTEREN_CHART_BINNEN_TEMPERATUUR_Yaxis2,  mintemp, maxtemp);
  lv_scale_set_range(ui_GISTEREN_CHART_TEMPERATUUR_LABELS_Yaxis1,  mintemp, maxtemp);
  lv_scale_set_range(ui_GISTEREN_CHART_TEMPERATUUR_LABELS_Yaxis2,  mintemp, maxtemp);
  lv_chart_set_range(ui_GISTEREN_CHART_BUITEN_TEMPERATUUR, LV_CHART_AXIS_PRIMARY_Y, mintemp, maxtemp);
  lv_chart_set_range(ui_GISTEREN_CHART_BUITEN_TEMPERATUUR, LV_CHART_AXIS_SECONDARY_Y, mintemp, maxtemp);
  lv_chart_set_range(ui_GISTEREN_CHART_BINNEN_TEMPERATUUR, LV_CHART_AXIS_PRIMARY_Y, mintemp, maxtemp);
  lv_chart_set_range(ui_GISTEREN_CHART_BINNEN_TEMPERATUUR, LV_CHART_AXIS_SECONDARY_Y, mintemp, maxtemp);
  lv_chart_set_range(ui_GISTEREN_CHART_TEMPERATUUR_LABELS, LV_CHART_AXIS_PRIMARY_Y, mintemp, maxtemp);
  lv_chart_set_range(ui_GISTEREN_CHART_TEMPERATUUR_LABELS, LV_CHART_AXIS_SECONDARY_Y, mintemp, maxtemp);

  lv_label_set_text(ui_NAN_RAAM_OOST, myObject[23]["NaN_times"]);
  lv_label_set_text(ui_NAN_RAAM_WEST, myObject[23]["NaN_times"]);
  lv_label_set_text(ui_NAN_GORDIJN_OOST, myObject[22]["NaN_times"]);
  lv_label_set_text(ui_NAN_GORDIJN_WEST, myObject[21]["NaN_times"]);
  lv_label_set_text(ui_NAN_SCHADUW_OOST, myObject[20]["NaN_times"]);
  lv_label_set_text(ui_NAN_SCHADUW_WEST, myObject[19]["NaN_times"]);
  // set values for the interface charts
  for (int i = 0; i < 24; i++) {
    lv_chart_series_t * ui_GISTEREN_CHART_BUITEN_TEMPERATUUR_series_1 = lv_chart_get_series_next(ui_GISTEREN_CHART_BUITEN_TEMPERATUUR, NULL);
    lv_chart_set_next_value(ui_GISTEREN_CHART_BUITEN_TEMPERATUUR, ui_GISTEREN_CHART_BUITEN_TEMPERATUUR_series_1, (double) myObject[i]["Temperature_outdoor"]);
    lv_chart_series_t * ui_GISTEREN_CHART_BINNEN_TEMPERATUUR_series_1 = lv_chart_get_series_next(ui_GISTEREN_CHART_BINNEN_TEMPERATUUR, NULL);
    lv_chart_set_next_value(ui_GISTEREN_CHART_BINNEN_TEMPERATUUR, ui_GISTEREN_CHART_BINNEN_TEMPERATUUR_series_1, (double) myObject[i]["Temperature_indoor"]);
    lv_chart_series_t * ui_GISTEREN_CHART_RAAM_OOST_series_1 = lv_chart_get_series_next(ui_GISTEREN_CHART_RAAM_OOST, NULL);
    lv_chart_set_next_value(ui_GISTEREN_CHART_RAAM_OOST, ui_GISTEREN_CHART_RAAM_OOST_series_1, (double) myObject[i]["windowdoor_voor"]);
    lv_chart_series_t * ui_GISTEREN_CHART_RAAM_WEST_series_1 = lv_chart_get_series_next(ui_GISTEREN_CHART_RAAM_WEST, NULL);
    lv_chart_set_next_value(ui_GISTEREN_CHART_RAAM_WEST, ui_GISTEREN_CHART_RAAM_WEST_series_1, (double) myObject[i]["windowdoor_achter"]);
    lv_chart_series_t * ui_GISTEREN_CHART_GORDIJN_OOST_series_1 = lv_chart_get_series_next(ui_GISTEREN_CHART_GORDIJN_OOST, NULL);
    lv_chart_set_next_value(ui_GISTEREN_CHART_GORDIJN_OOST, ui_GISTEREN_CHART_GORDIJN_OOST_series_1, (double) myObject[i]["curtain_voor"]);
    lv_chart_series_t * ui_GISTEREN_CHART_GORDIJN_WEST_series_1 = lv_chart_get_series_next(ui_GISTEREN_CHART_GORDIJN_WEST, NULL);
    lv_chart_set_next_value(ui_GISTEREN_CHART_GORDIJN_WEST, ui_GISTEREN_CHART_GORDIJN_WEST_series_1, (double) myObject[i]["curtain_achter"]);
    lv_chart_series_t * ui_GISTEREN_CHART_SCHADUW_OOST_series_1_array = lv_chart_get_series_next(ui_GISTEREN_CHART_SCHADUW_OOST, NULL);
    lv_chart_set_next_value(ui_GISTEREN_CHART_SCHADUW_OOST, ui_GISTEREN_CHART_SCHADUW_OOST_series_1_array, (double) myObject[i]["shade_voor"]);
    lv_chart_series_t * ui_GISTEREN_CHART_SCHADUW_WEST_series_1 = lv_chart_get_series_next(ui_GISTEREN_CHART_SCHADUW_WEST, NULL);
    lv_chart_set_next_value(ui_GISTEREN_CHART_SCHADUW_WEST, ui_GISTEREN_CHART_SCHADUW_WEST_series_1, (double) myObject[i]["shade_achter"]);
  }
}

void setup ()
{
  String LVGL_Arduino = String("LVGL Library Version: ") + lv_version_major() + "." + lv_version_minor() + "." + lv_version_patch();
  Serial.begin(115200);
  Serial.println(LVGL_Arduino);

  //////////////////////////////////////////// HTTP request start
  WiFi.begin(ssid, password);

  //////////////////////////////////////////// Start LVGL
  lv_init();
  // Register print function for debugging
  lv_log_register_print_cb(log_print);

  // Start the SPI for the touchscreen and init the touchscreen
  touchscreenSPI.begin(XPT2046_CLK, XPT2046_MISO, XPT2046_MOSI, XPT2046_CS);
  touchscreen.begin(touchscreenSPI);
  // Set the Touchscreen rotation in landscape mode
  // Note: in some displays, the touchscreen might be upside down, so you might need to set the rotation to 1: touchscreen.setRotation(1);
  touchscreen.setRotation(0);

  // Create a display object
  lv_display_t * disp;
  // Initialize the TFT display using the TFT_eSPI library  //////////////////////////////////////////////////////////// KEEP
  disp = lv_tft_espi_create(SCREEN_WIDTH, SCREEN_HEIGHT, draw_buf, sizeof(draw_buf));

  // lv_display_set_rotation(disp, LV_DISPLAY_ROTATION_90)
  tft.begin();
  tft.setRotation(0);

  // Initialize an LVGL input device object (Touchscreen)
  lv_indev_t * indev = lv_indev_create();
  lv_indev_set_type(indev, LV_INDEV_TYPE_POINTER);
  // Set the callback function to read Touchscreen input
  lv_indev_set_read_cb(indev, touchscreen_read);

  ui_init(); /////////////////////////////////////////////// this calls the ui I made in squareline, export ui files to ui file in arduino library

}

unsigned long timer = 0;

void loop ()
{
  // // lv_timer_handler(); /* let the GUI do its work */
  lv_task_handler();  // let the GUI do its work
  lv_tick_inc(5);     // tell LVGL how much time has passed
  delay(5);           // let this time pass

  if(touchscreen.tirqTouched() && touchscreen.touched()){
  timer = millis();
  }
  else if(millis() - timer >= 60000){
    // Serial.println("Sleep…");
    _ui_screen_change(&ui_INACTIVITY, LV_SCR_LOAD_ANIM_NONE, 100, 0, &ui_INACTIVITY_screen_init);
    timer = 0;
  }
}

// comment out events in ui_events.c in ui src

//// SWAP THIS EVENT IN UI.C
// void ui_event_SETTINGS_RANGE_SLIDER(lv_event_t * e)
// {
//     lv_event_code_t event_code = lv_event_get_code(e);
//     lv_obj_t * target = lv_event_get_target(e);
//     if(event_code == LV_EVENT_VALUE_CHANGED) {
//         char buf_top[4];
//         lv_snprintf(buf_top, sizeof(buf_top), "%d", (int)lv_slider_get_value(target));
//         lv_label_set_text(ui_SETTINGS_RANGE_TOP, buf_top);

//     }
//     if(event_code == LV_EVENT_VALUE_CHANGED) {
//         char buf_bottom[4];
//         lv_snprintf(buf_bottom, sizeof(buf_bottom), "%d", (int)lv_slider_get_left_value(target));
//         lv_label_set_text(ui_SETTINGS_RANGE_BOTTOM, buf_bottom);
//     }
// }
