EmiliaViaene/Un-designing-a-Thermal-Prediction-System/documentation/images/IMG_2468.jpg

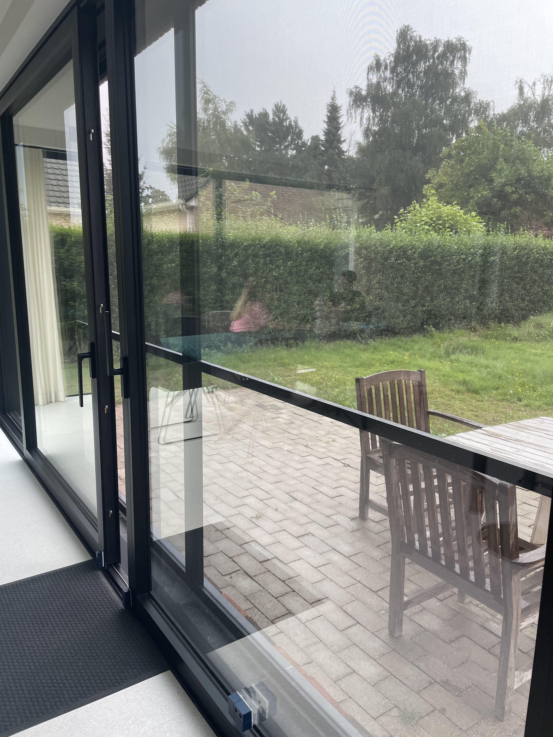
documentation/images/IMG_2468.jpg
