EmiliaViaene/Un-designing-a-Thermal-Prediction-System/documentation/images/IMG_3575.jpg

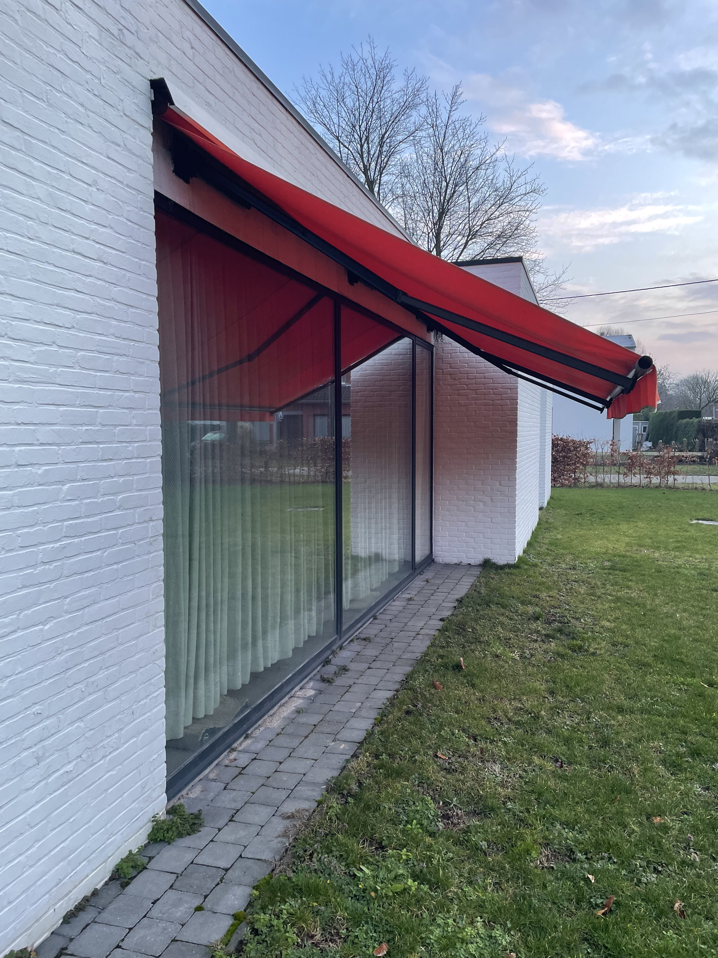
documentation/images/IMG_3575.jpg
